RT-CUSTOMZ/WortUhr/Media/Rückseite.jpg

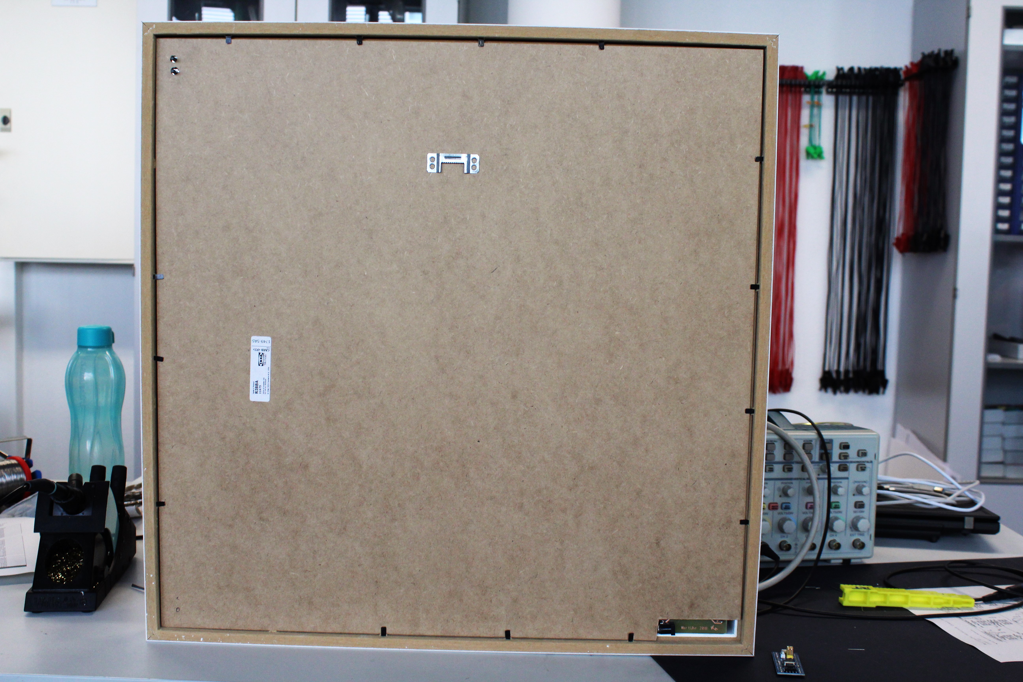
Media/Rückseite.jpg
