RT-CUSTOMZ/WortUhr/Media/Gitter Aufbau.png

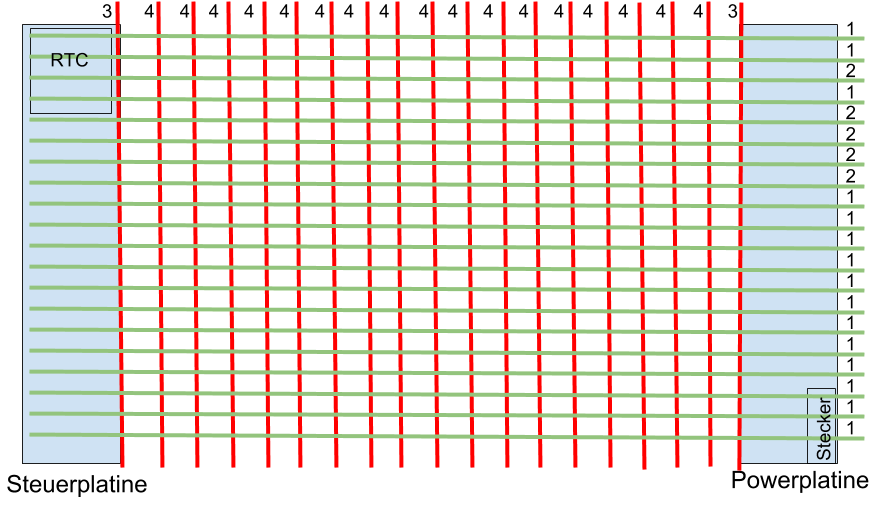
Media/Gitter Aufbau.png
