RT-CUSTOMZ/WortUhr/Hardware/Steuerplatine-Fertigung/Fertigungsplatine/Produktionsdaten_Steuerplatine_V2.2-Fertigung/Additional Documentation.pdf

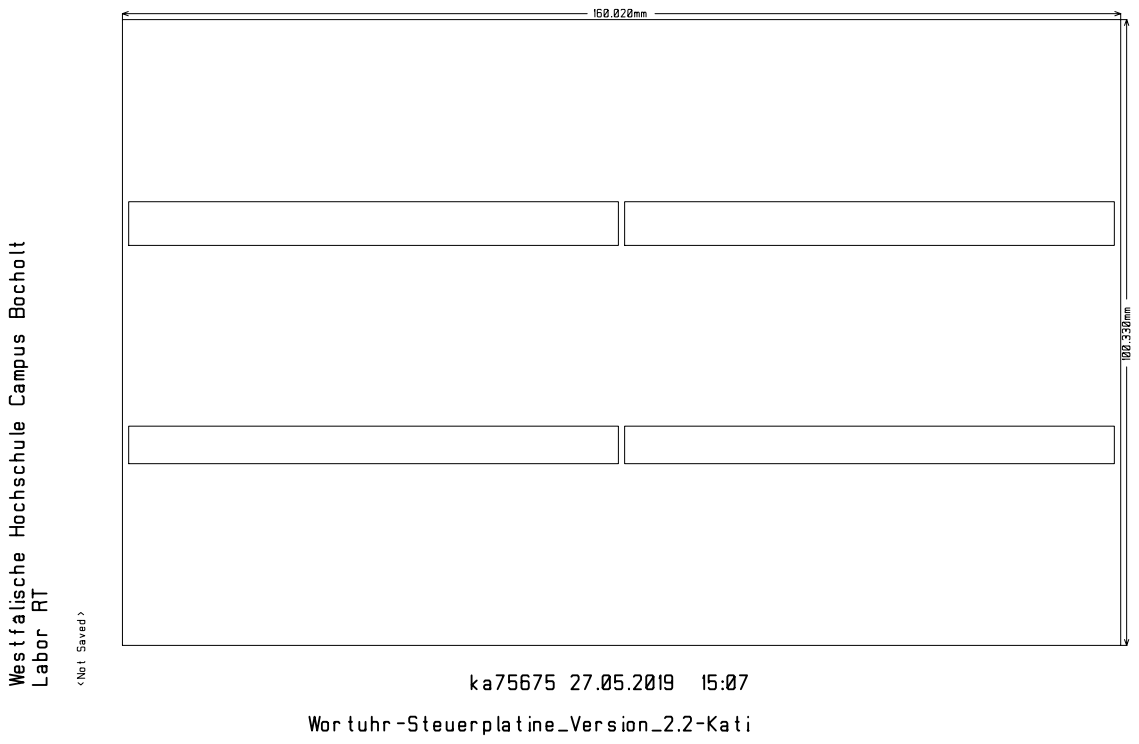
[picture p24: page 1]
