RT-CUSTOMZ/WortUhr/Hardware/Steuerplatine-Fertigung/Fertigungsplatine/Produktionsdaten_Steuerplatine_V2.2-Fertigung/Bottom Bestückungsplan.pdf

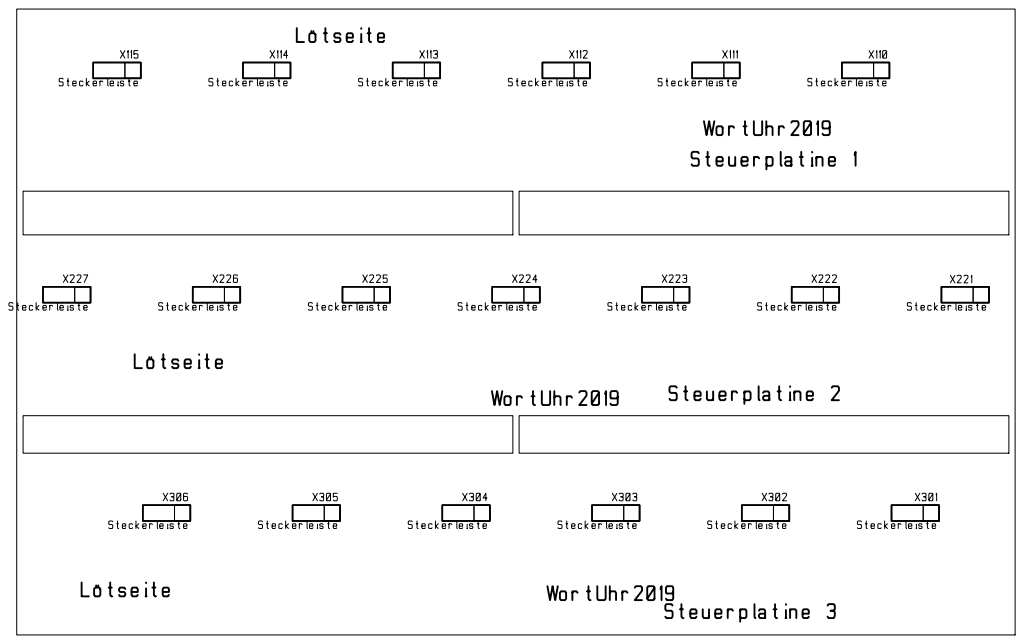
[picture p25: page 1]
