RT-CUSTOMZ/WortUhr/Hardware/Steuerplatine-Fertigung/Fertigungsplatine/Produktionsdaten_Steuerplatine_V2.2-Fertigung/Bottom Copper.pdf

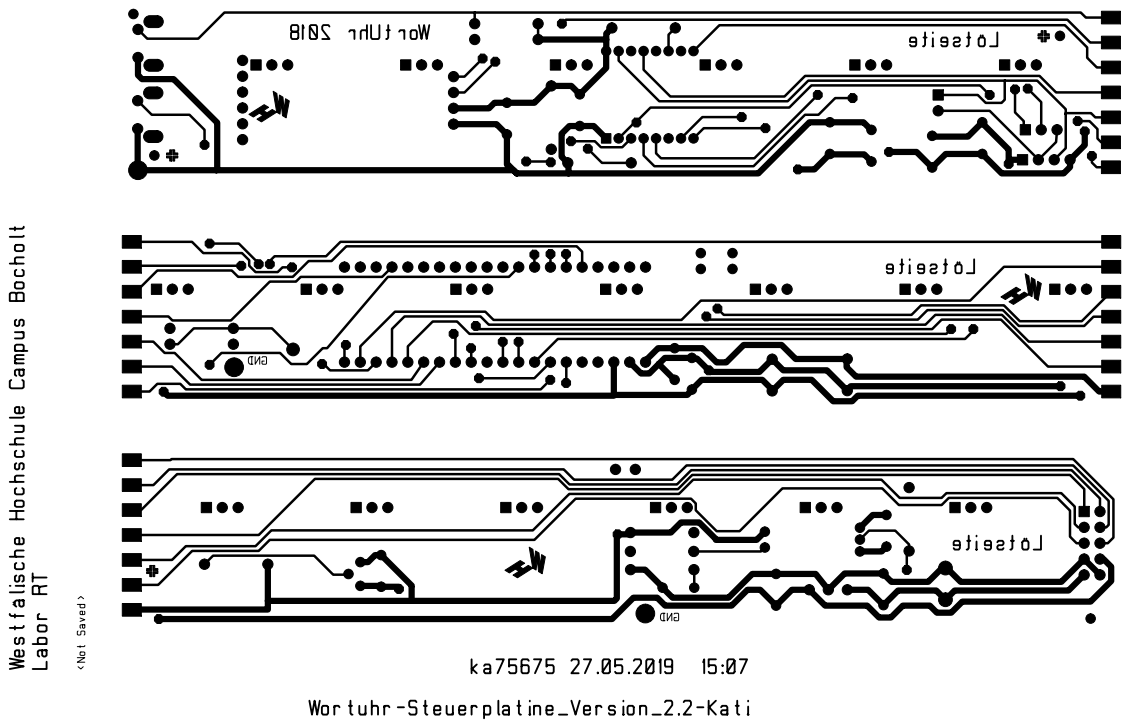
[picture p26: page 1]
