RT-CUSTOMZ/WortUhr/Hardware/Steuerplatine-Fertigung/Fertigungsplatine/Produktionsdaten_Steuerplatine_V2.2-Fertigung/Bottom Silkscreen.pdf

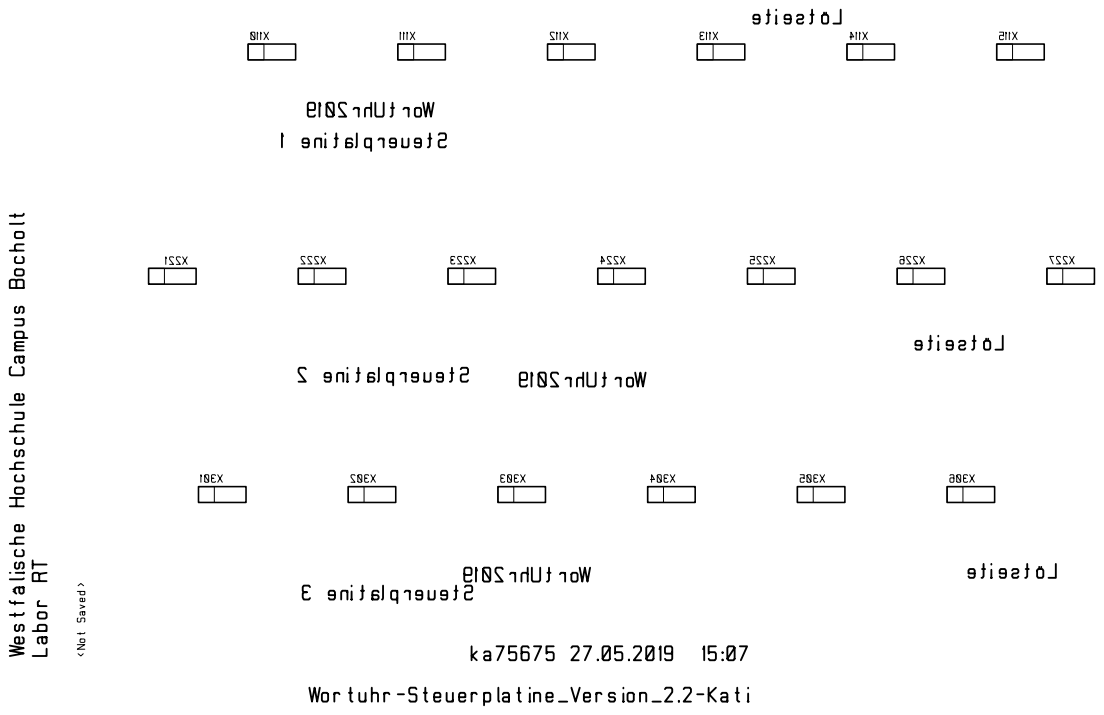
[picture p27: page 1]
