RT-CUSTOMZ/WortUhr/Hardware/Steuerplatine-Fertigung/Fertigungsplatine/Produktionsdaten_Steuerplatine_V2.2-Fertigung/Bottom Solderresist.pdf

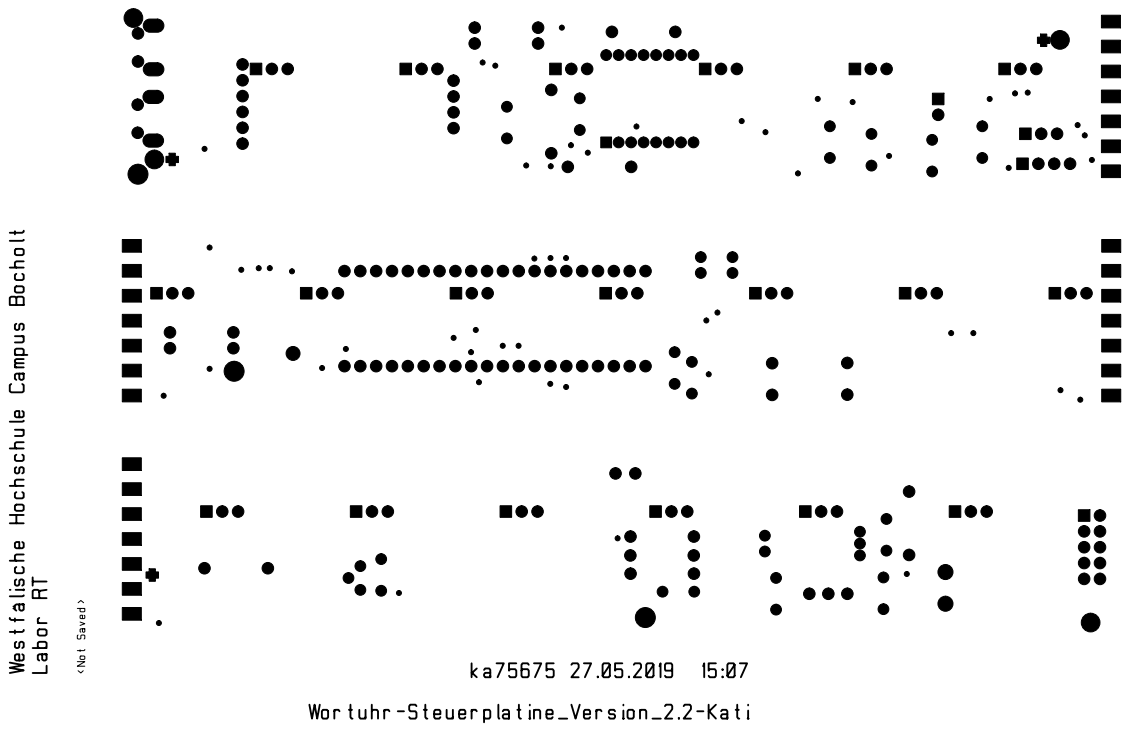
[picture p28: page 1]
