RT-CUSTOMZ/WortUhr/Hardware/Steuerplatine-Fertigung/Fertigungsplatine/Produktionsdaten_Steuerplatine_V2.2-Fertigung/Schaltplan-Fertigung-Steuer.pdf

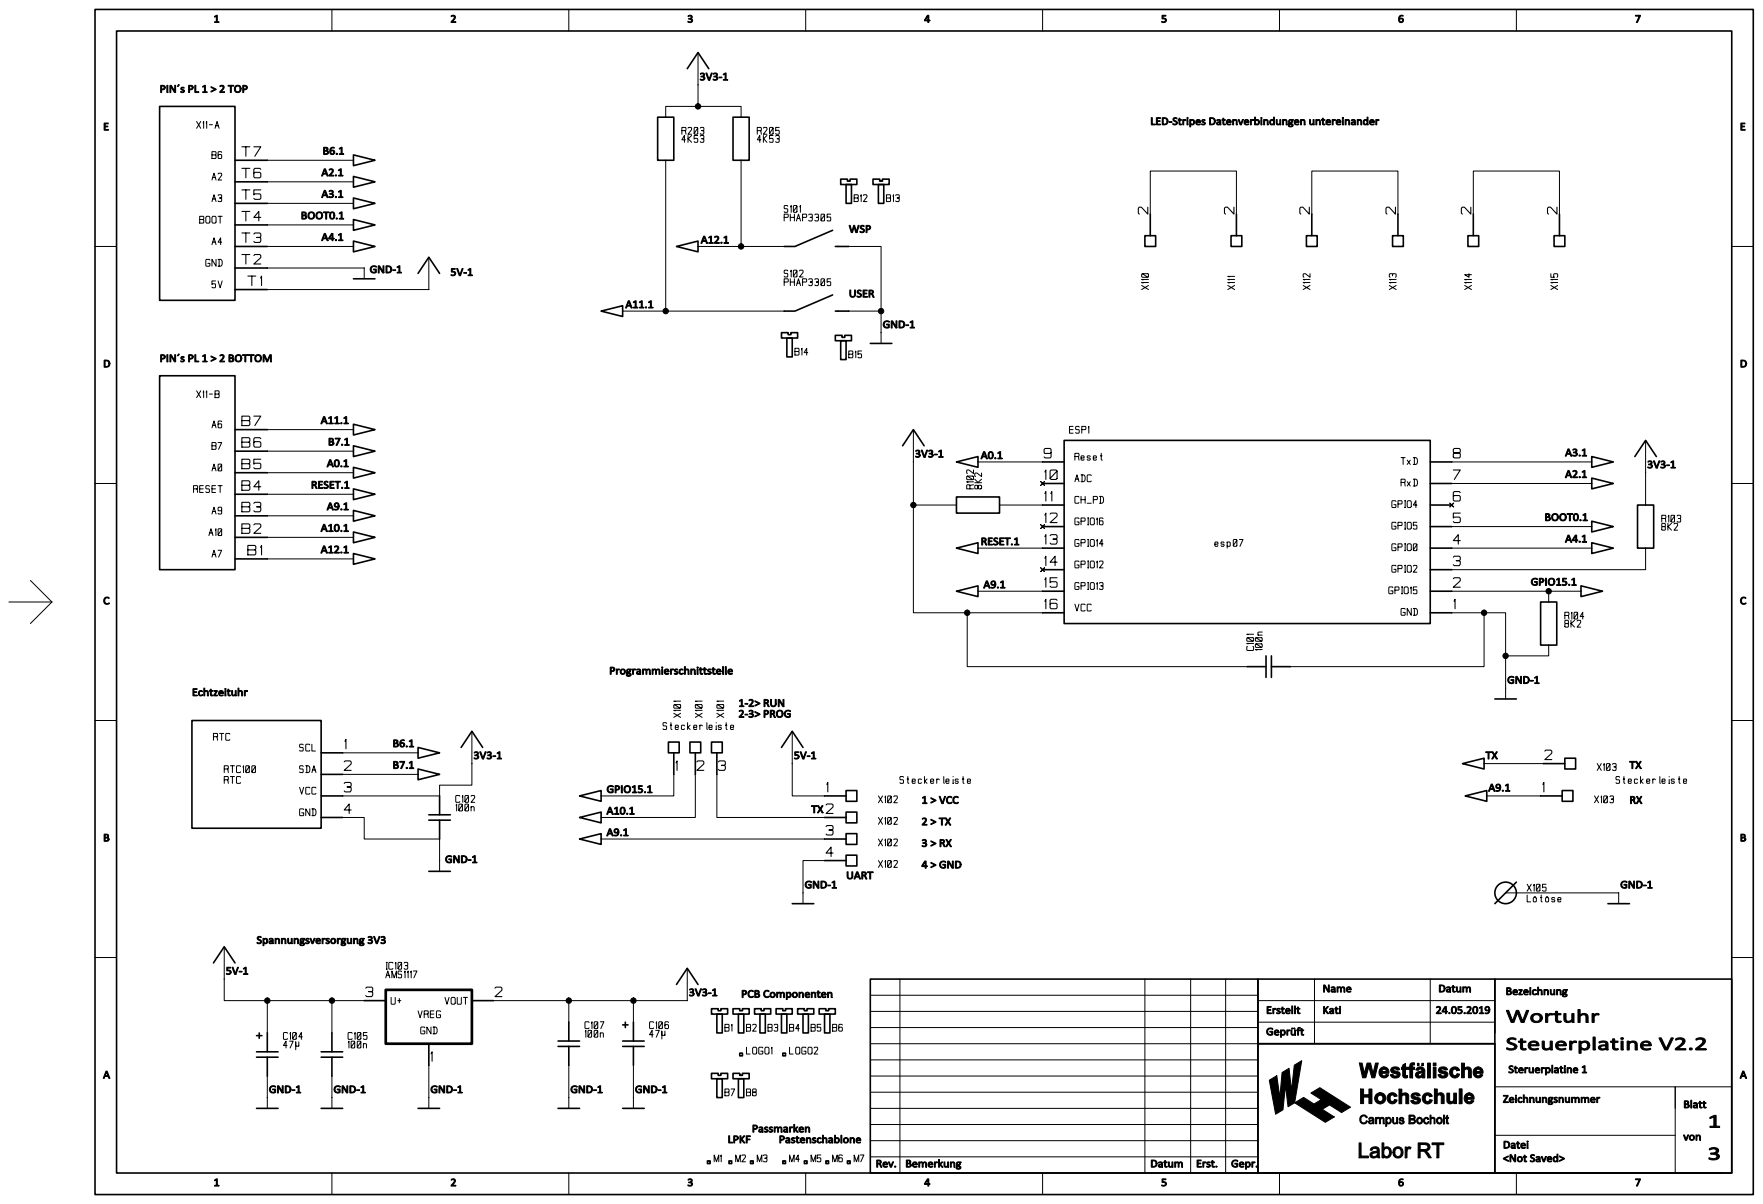
[picture p29: page 1]

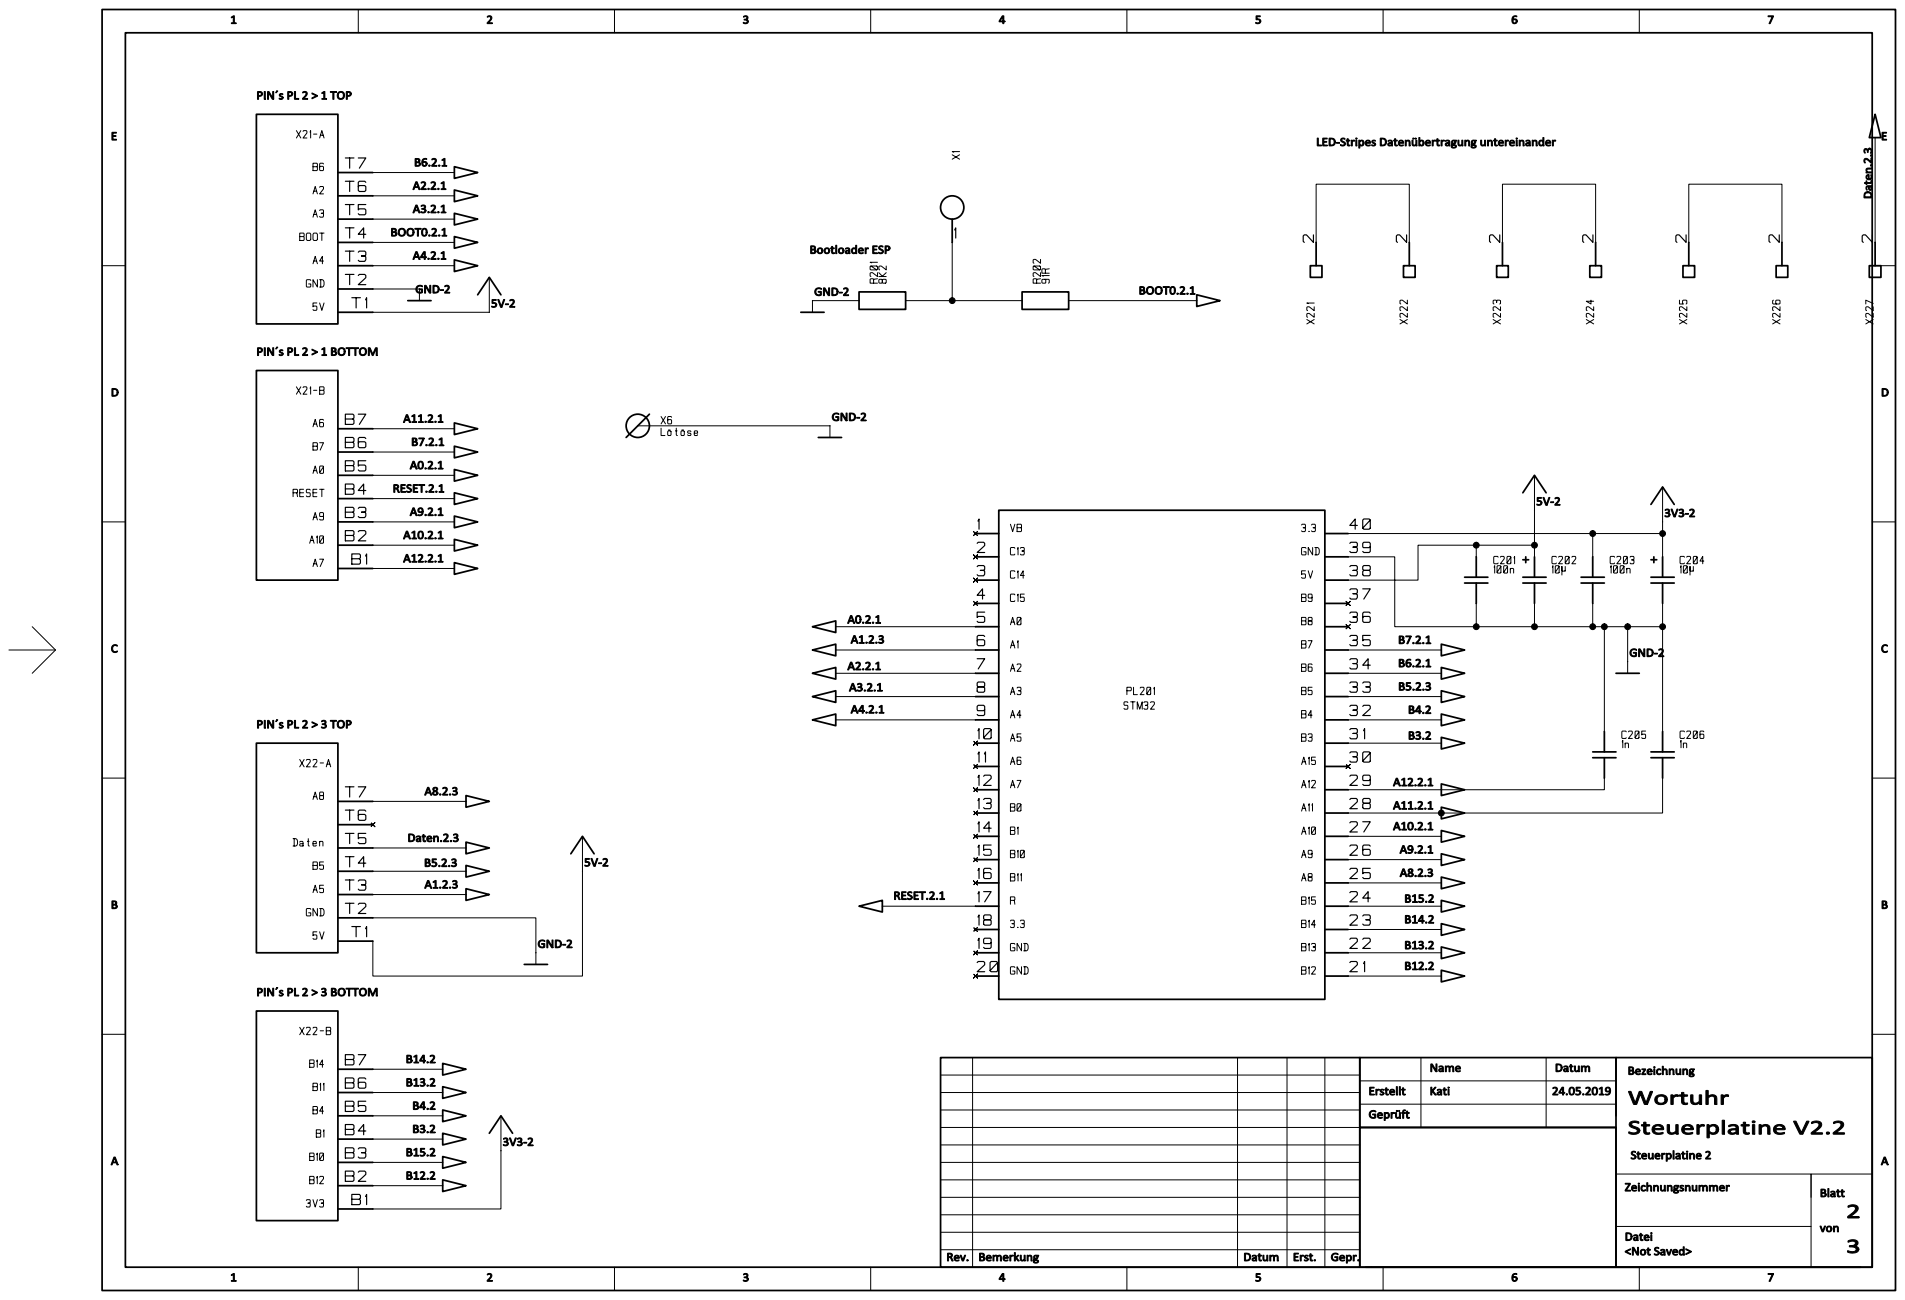
[picture p30: page 2]

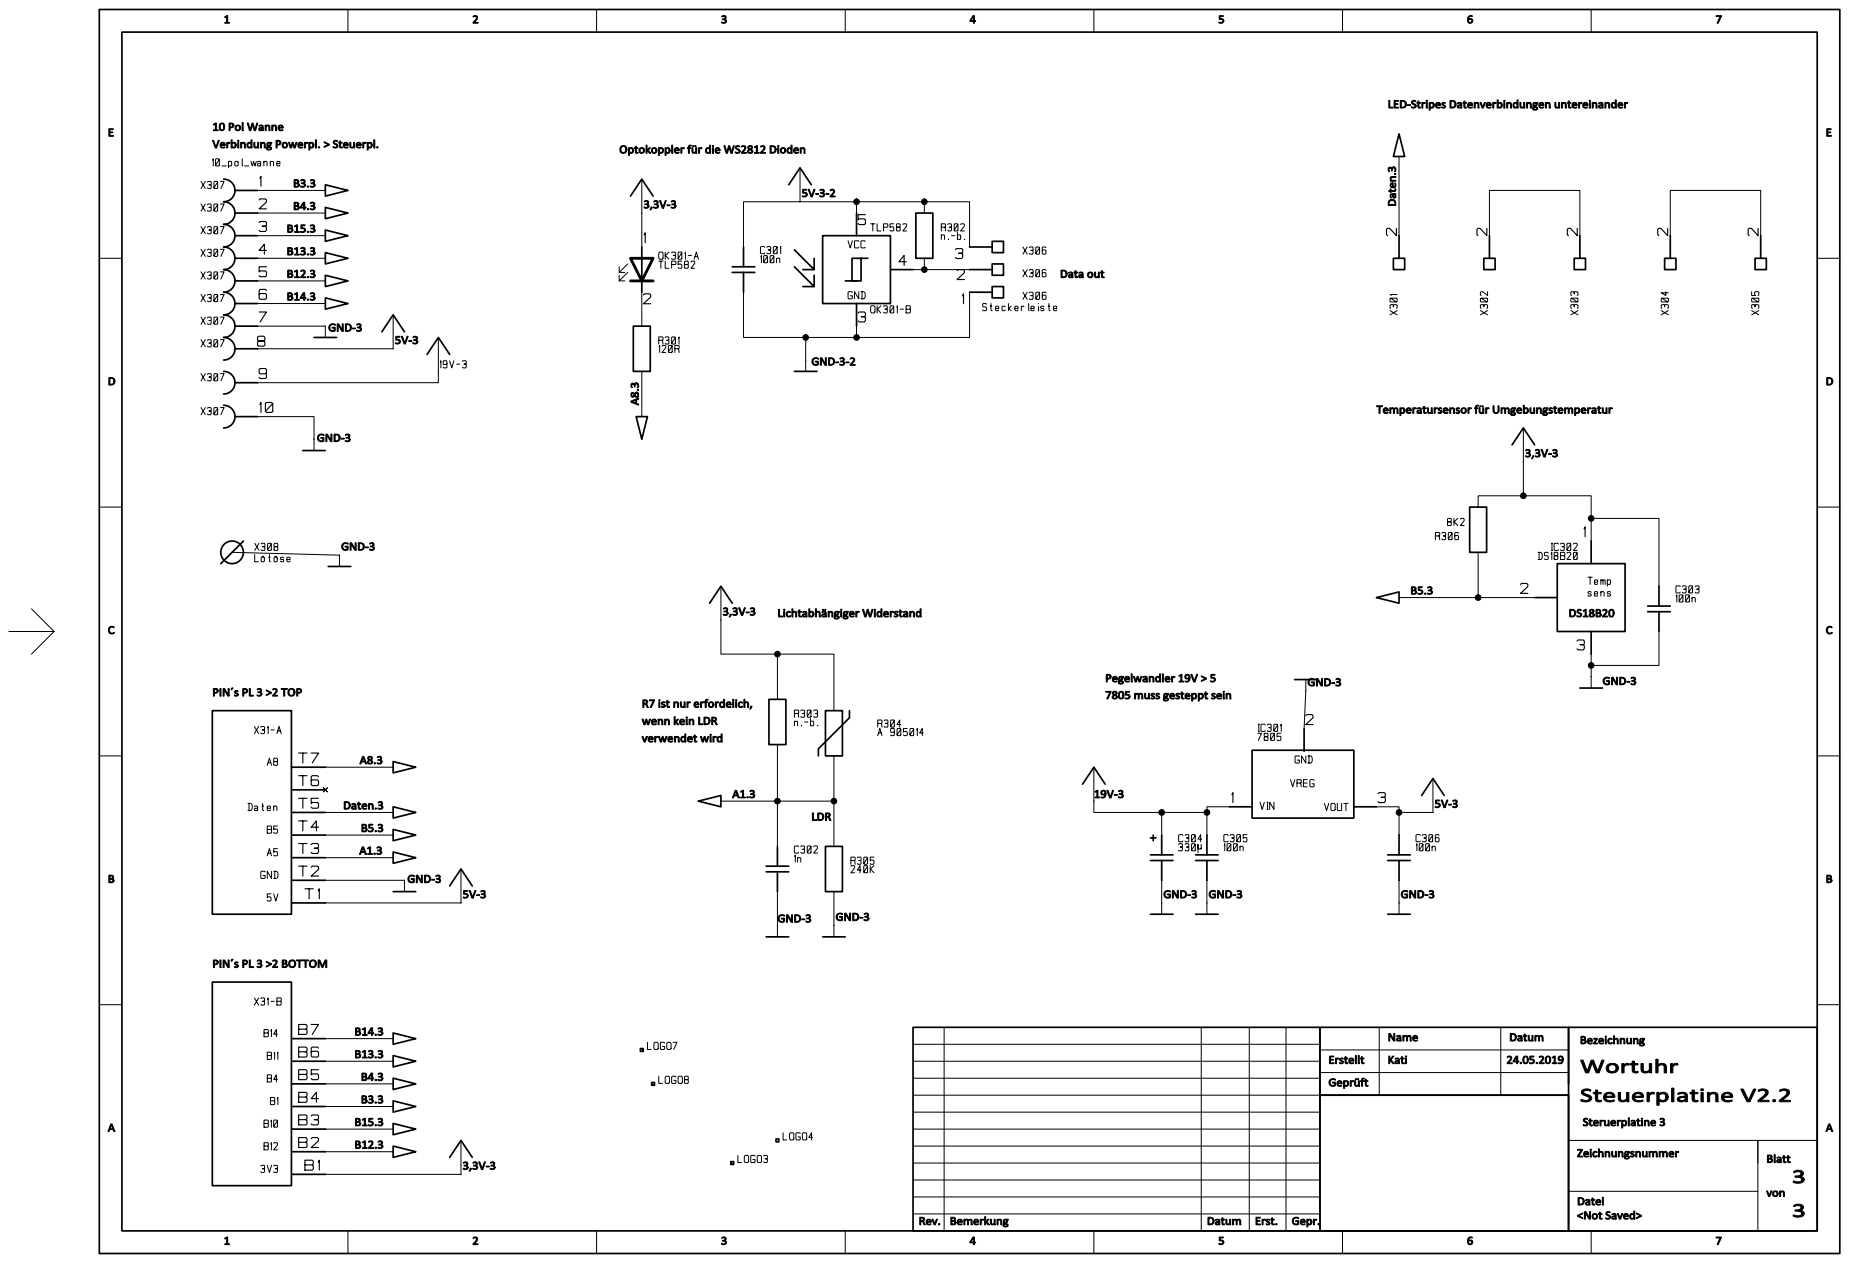
[picture p31: page 3]
