RT-CUSTOMZ/WortUhr/Lasercutter/Gitter-2x3-7x4.pdf

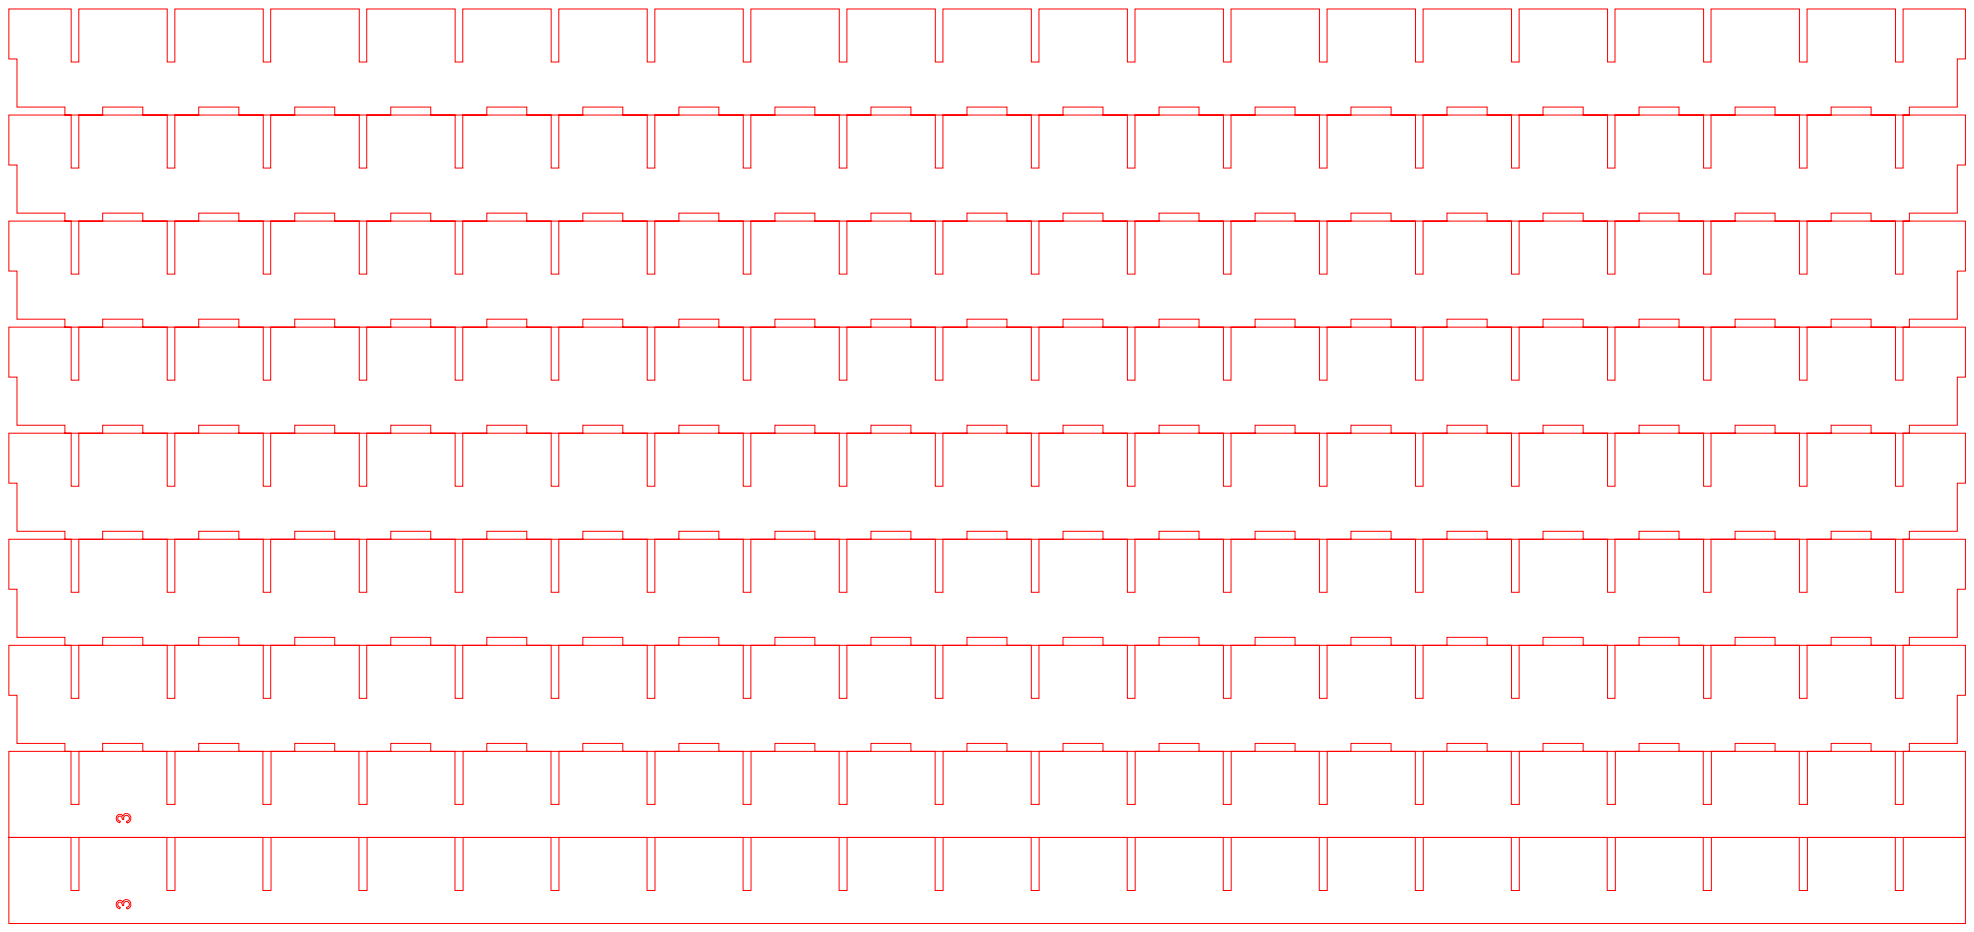
[picture p36: page 1]
