RT-CUSTOMZ/WortUhr/Lasercutter/Gitter-5x1-5x2.pdf

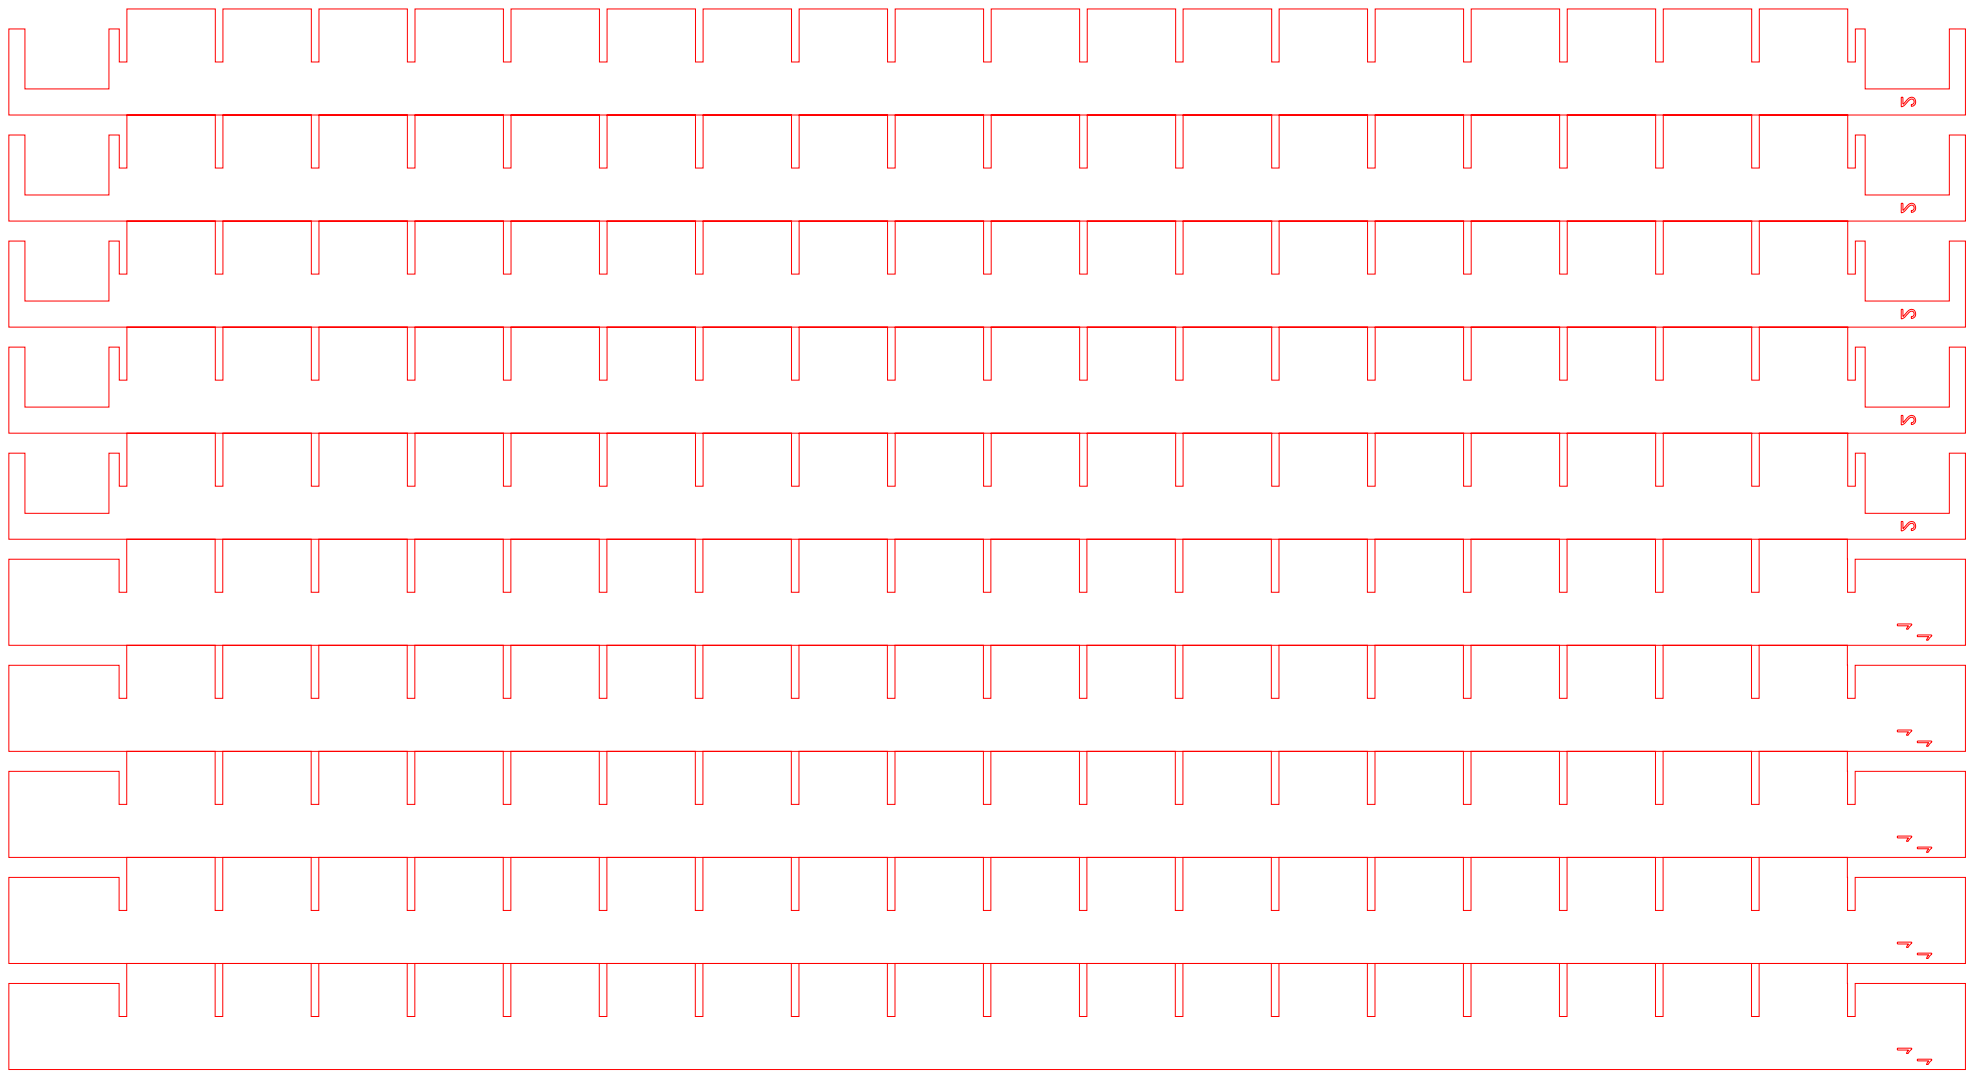
[picture p37: page 1]
