RT-CUSTOMZ/WortUhr/Hardware/Alt/Netzteilplatinen V1.1/Doku Bestückungsplan BOTTOM.pdf

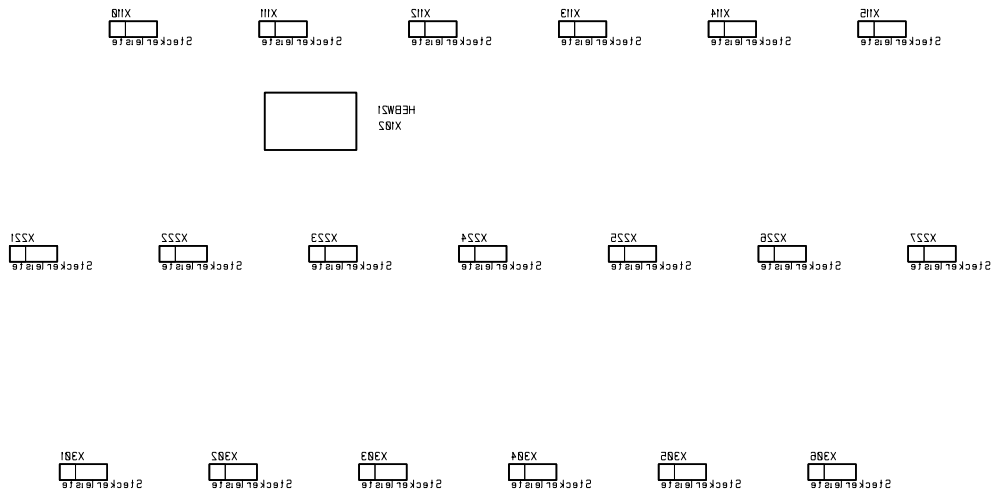
[picture p38: page 1]
