RT-CUSTOMZ/WortUhr/Hardware/Alt/Netzteilplatinen V1.1/Doku Bestückungsplan TOP.pdf

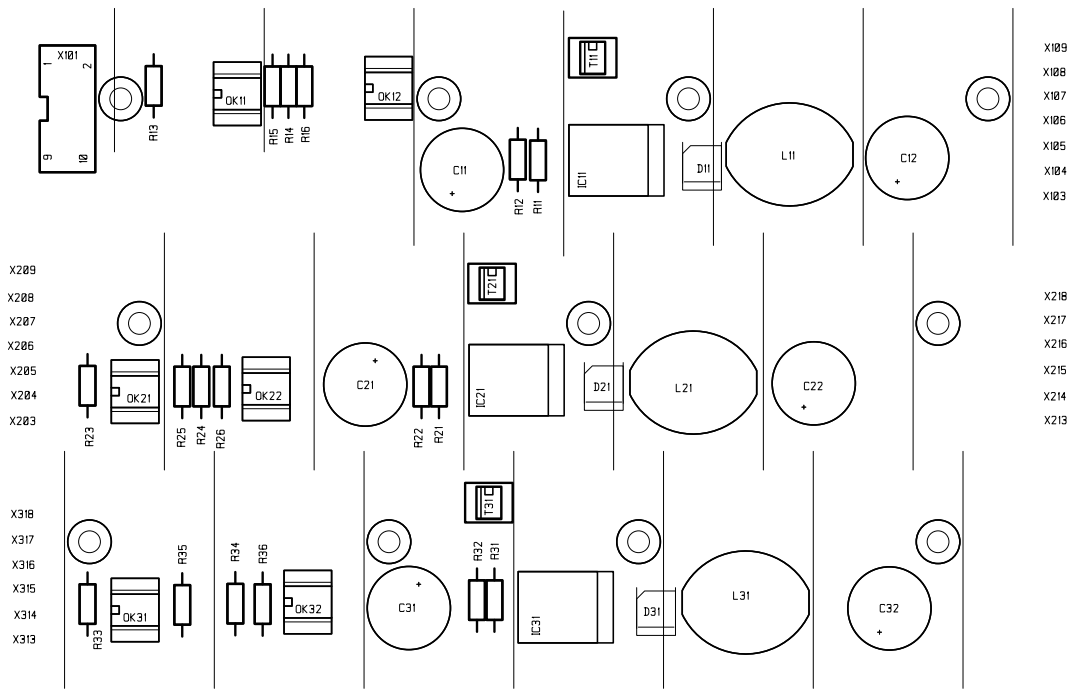
[picture p39: page 1]
