RT-CUSTOMZ/WortUhr/Hardware/Alt/Netzteilplatinen V1.1/Doku Routingübertsicht BOTTOM.pdf

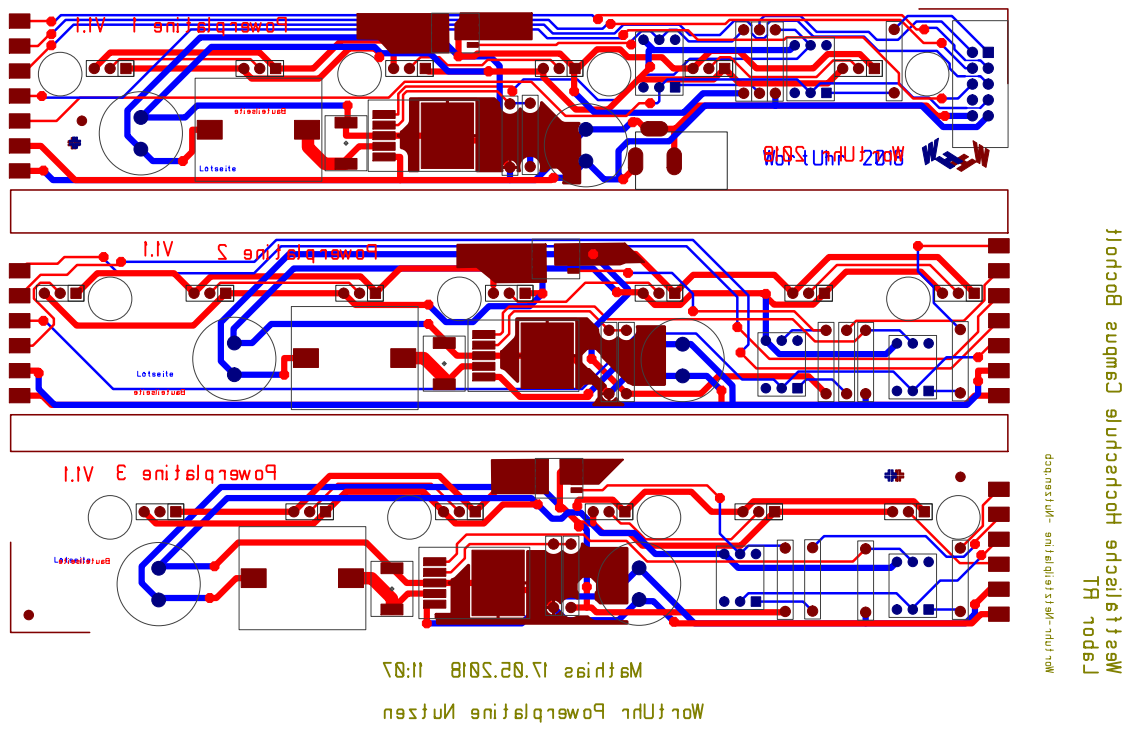
[picture p40: page 1]
