RT-CUSTOMZ/WortUhr/Hardware/Alt/Netzteilplatinen V1.1/Doku Routingübertsicht TOP.pdf

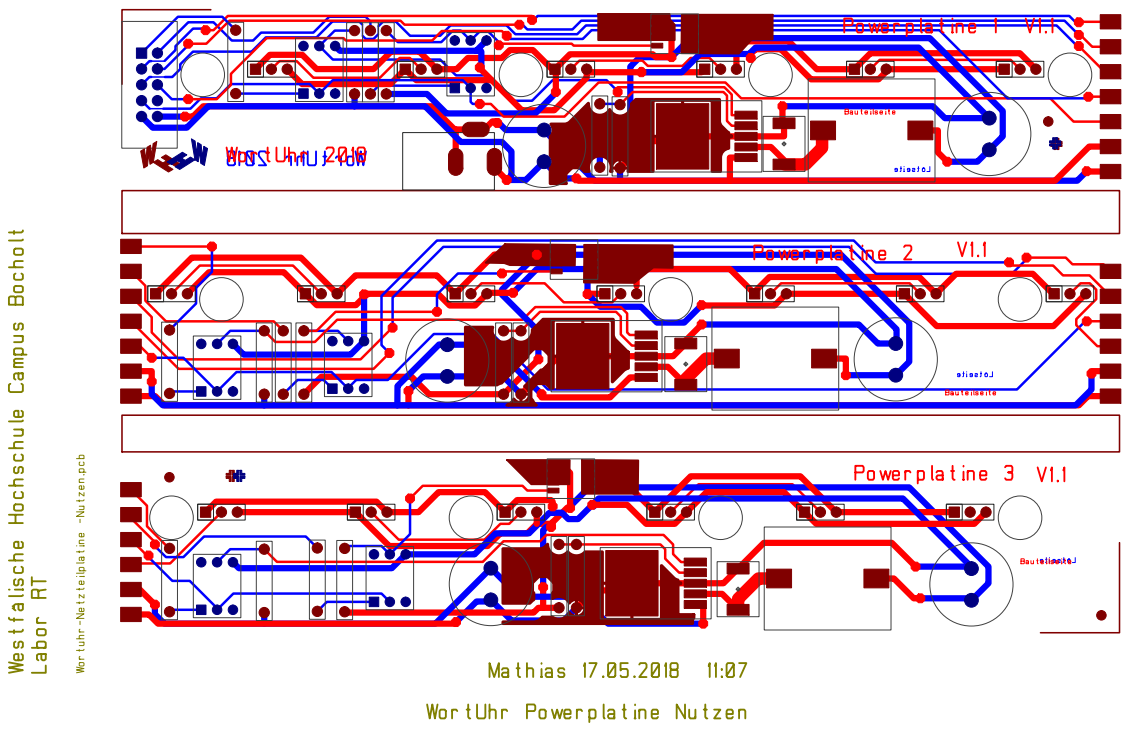
[picture p41: page 1]
