RT-CUSTOMZ/WortUhr/Hardware/Alt/Netzteilplatinen V1.1/Film Bestückungsplan TOP in Kupfer.pdf

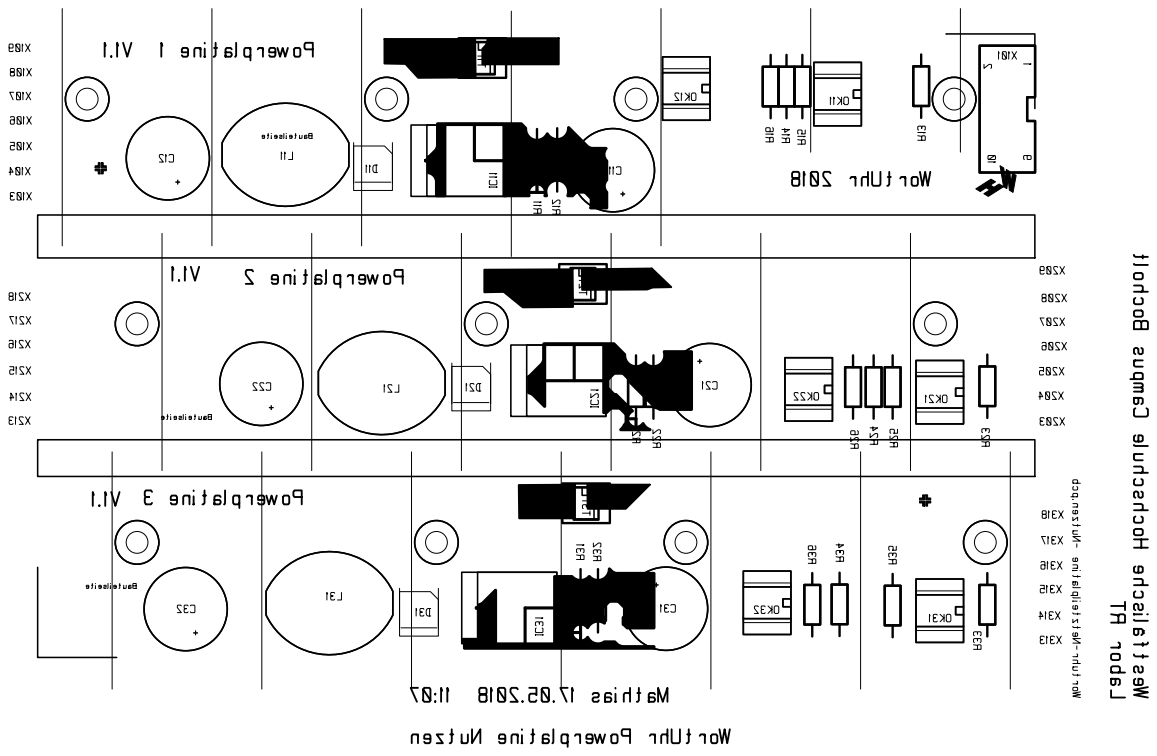
[picture p42: page 1]
