RT-CUSTOMZ/WortUhr/Hardware/Alt/Netzteilplatinen V1.1/FILM BOTTOM.pdf

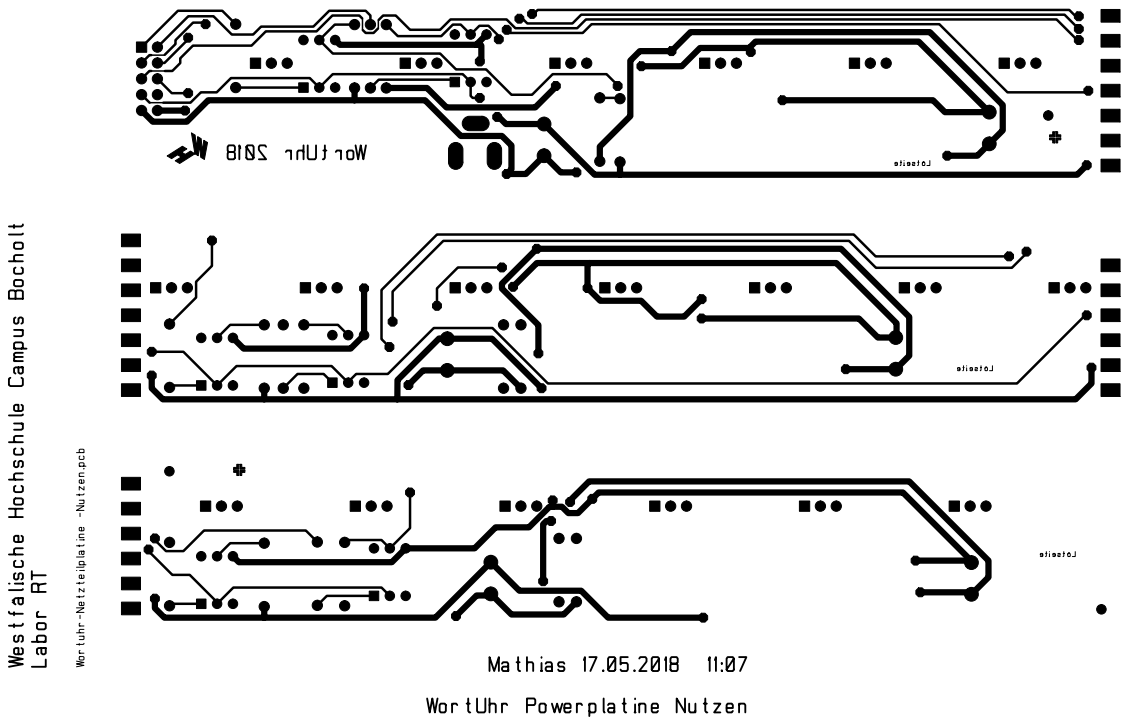
[picture p43: page 1]
