RT-CUSTOMZ/WortUhr/Hardware/Alt/Netzteilplatinen V1.1/FILM TOP.pdf

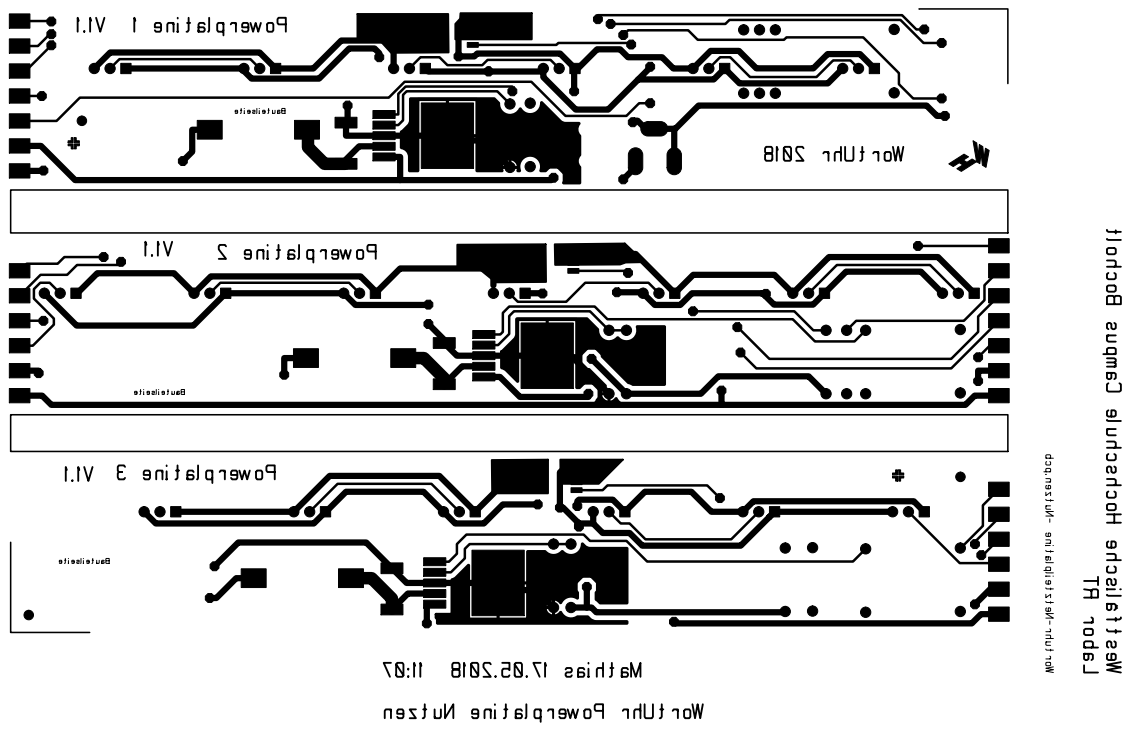
[picture p44: page 1]
