RT-CUSTOMZ/WortUhr/Hardware/Alt/Netzteilplatinen V1.1/Wortuhr-Netzteilplatine -Nutzen-Bestück Bottom.pdf

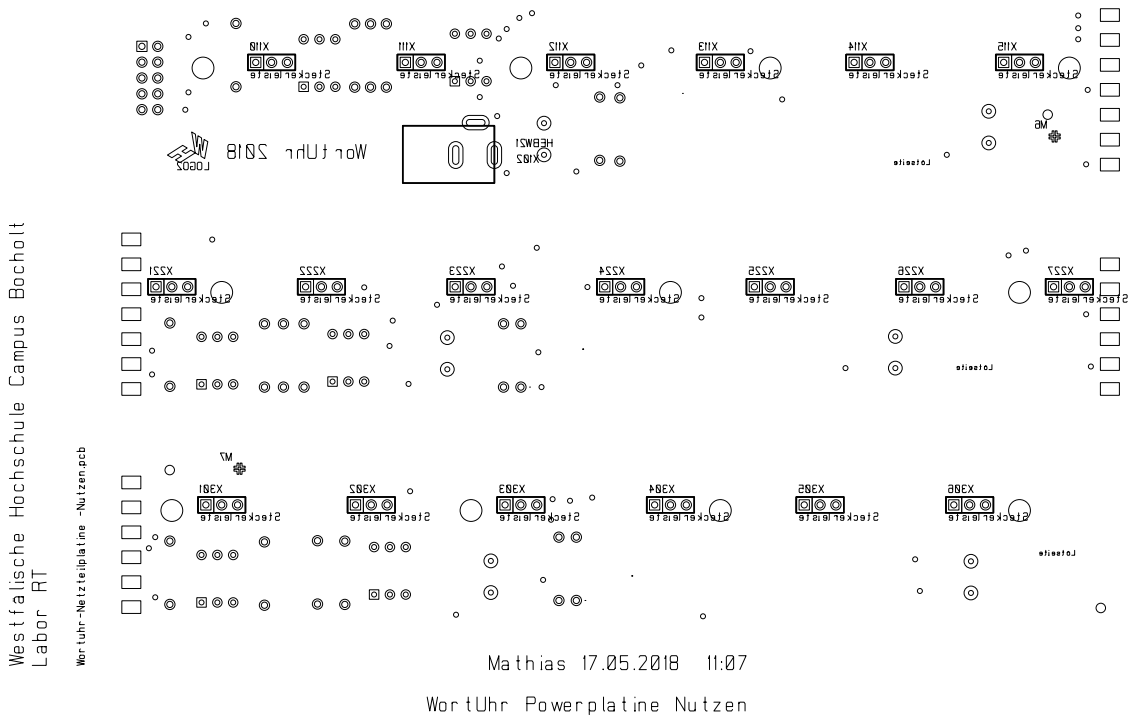
[picture p45: page 1]
