RT-CUSTOMZ/WortUhr/Hardware/Alt/Netzteilplatinen V1.1/Wortuhr-Netzteilplatine -Nutzen-Bestück Top.pdf

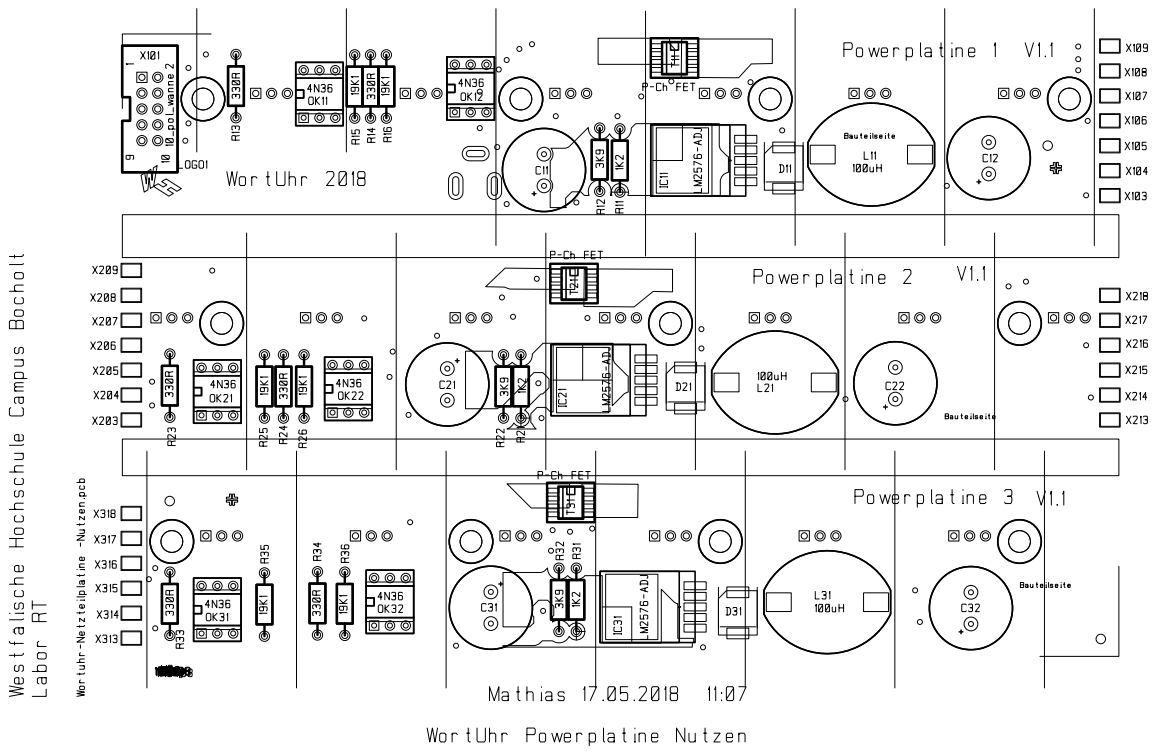
[picture p46: page 1]
