RT-CUSTOMZ/WortUhr/Hardware/Alt/Netzteilplatinen V1.1/Wortuhr-Netzteilplatine -Nutzen-Schematic.pdf

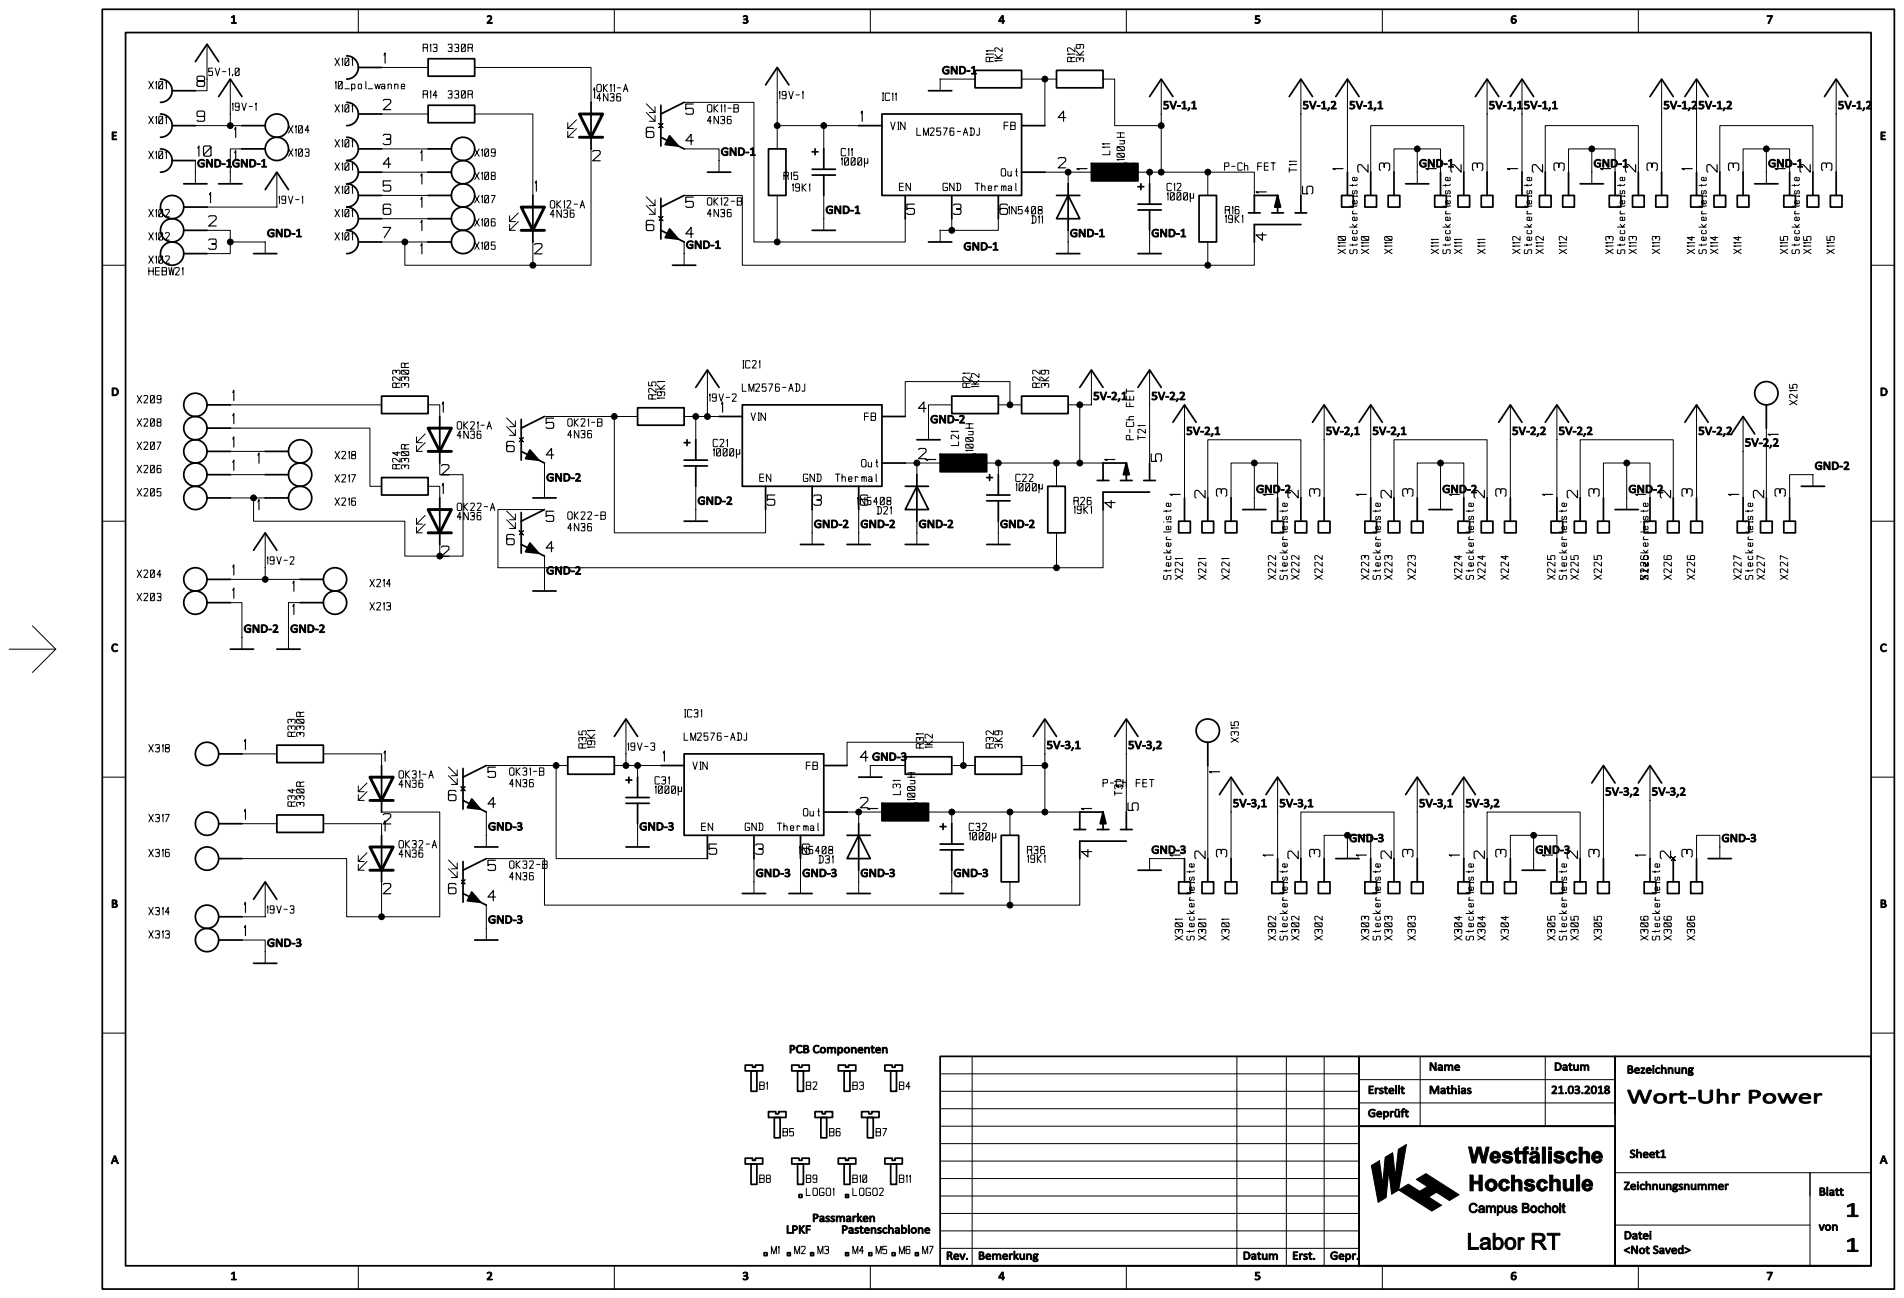
[picture p47: page 1]
