RT-CUSTOMZ/WortUhr/Hardware/Alt/Netzteilplatinen V1.1/Wortuhr-Netzteilplatine -Nutzen-Viaplan.pdf

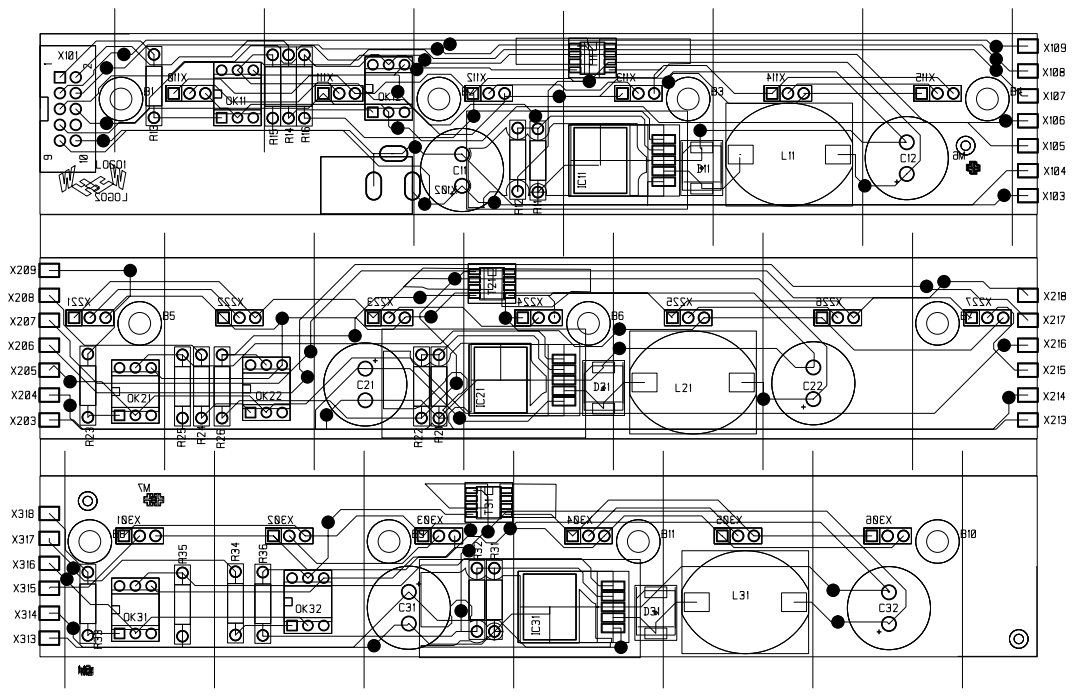
[picture p48: page 1]
