RT-CUSTOMZ/WortUhr/Hardware/Alt/Steuerplatinen Produktionsdaten V1.1/Doku Bestückungsplan BOTTOM.pdf

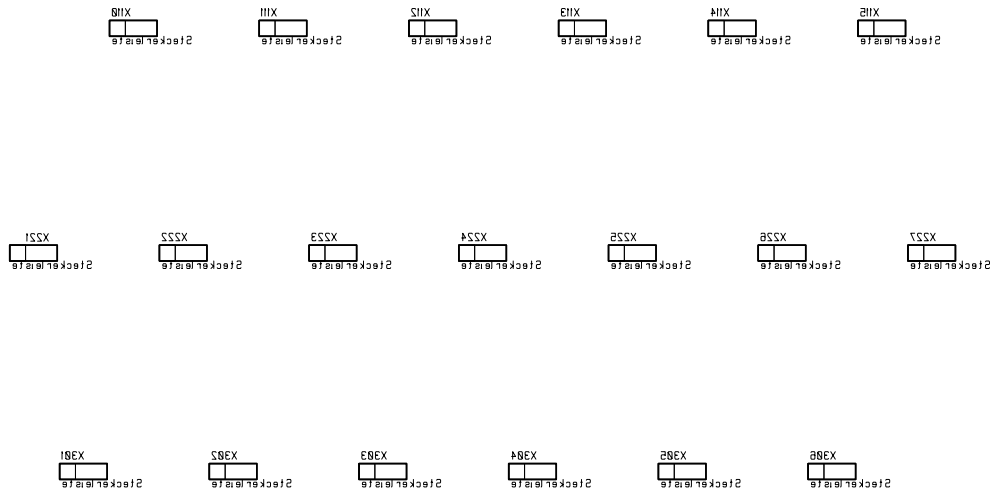
[picture p49: page 1]
