RT-CUSTOMZ/WortUhr/Hardware/Alt/Steuerplatinen Produktionsdaten V1.1/Doku Bestückungsplan TOP.pdf

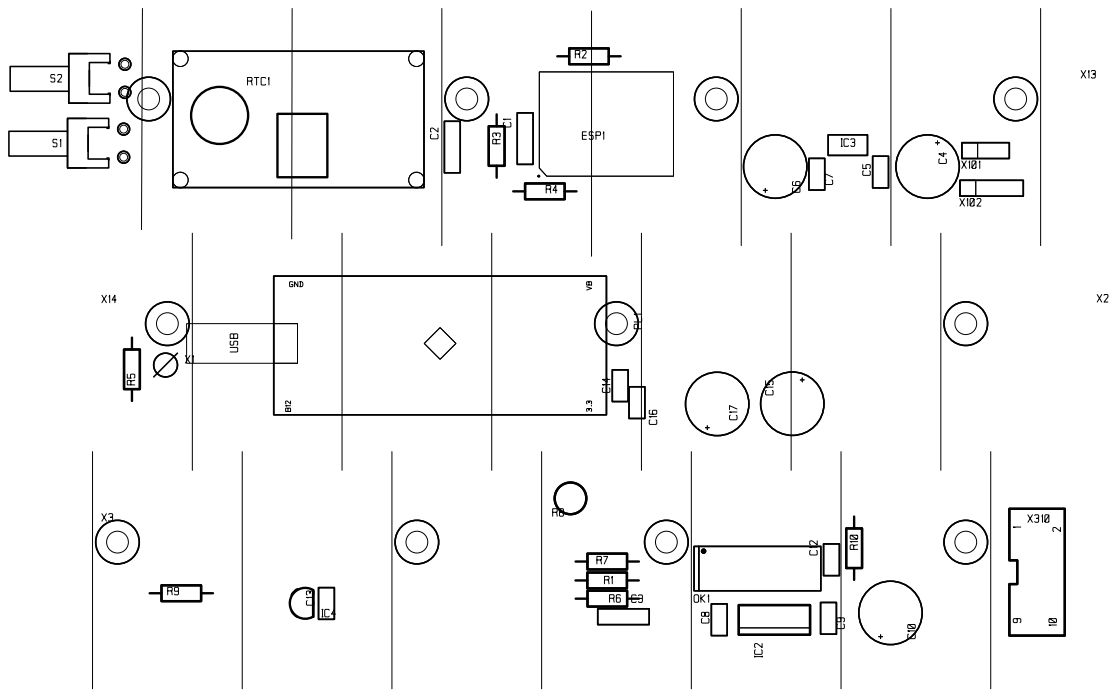
[picture p50: page 1]
