RT-CUSTOMZ/WortUhr/Hardware/Alt/Steuerplatinen Produktionsdaten V1.1/Doku Routingübertsicht BOTTOM.pdf

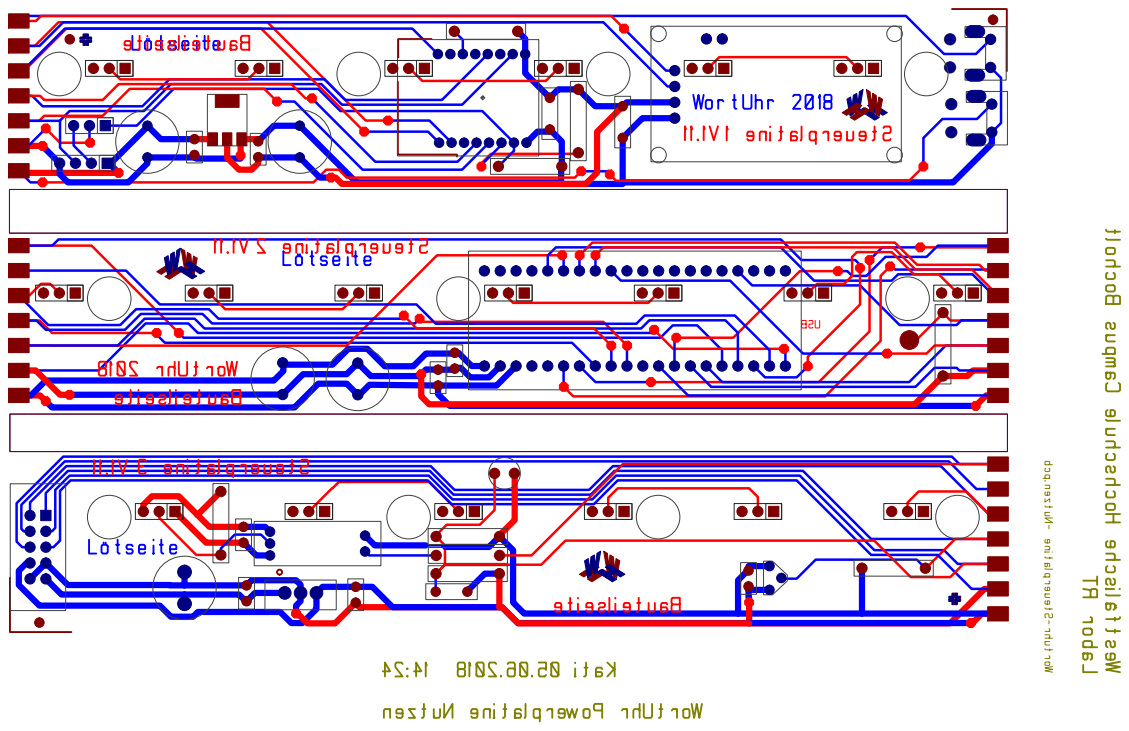
[picture p51: page 1]
