RT-CUSTOMZ/WortUhr/Hardware/Alt/Steuerplatinen Produktionsdaten V1.1/Doku Routingübertsicht TOP.pdf

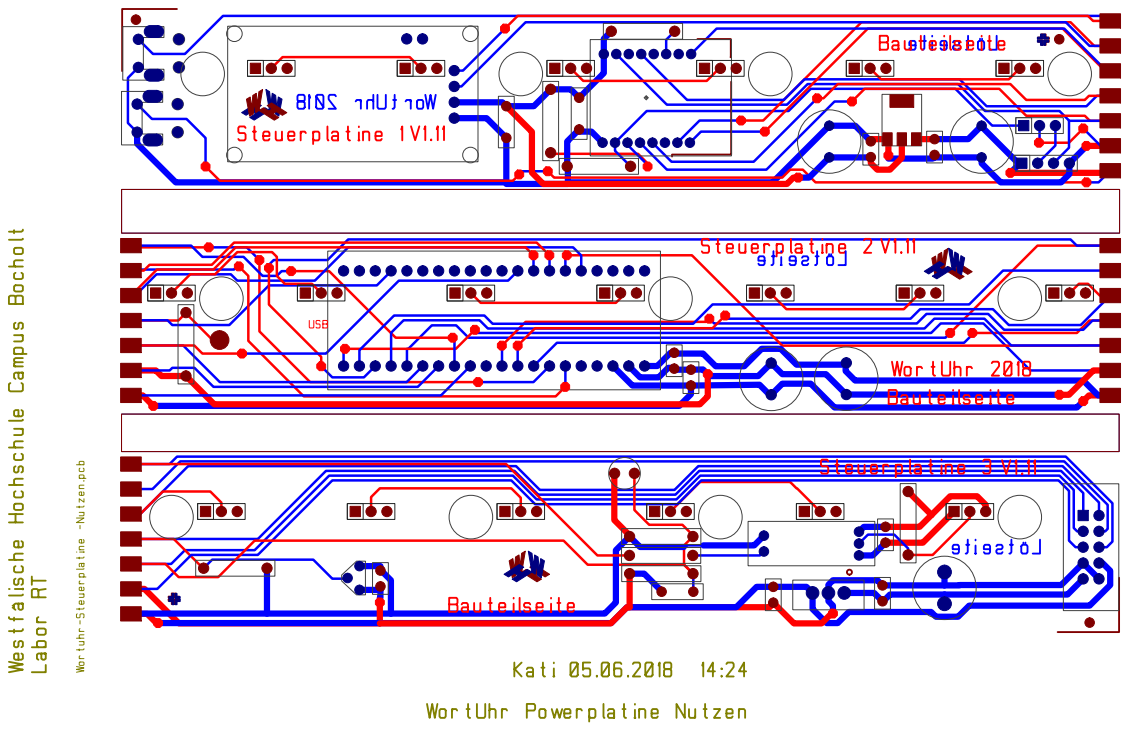
[picture p52: page 1]
