RT-CUSTOMZ/WortUhr/Hardware/Alt/Steuerplatinen Produktionsdaten V1.1/Film Bestückungsplan TOP in Kupfer.pdf

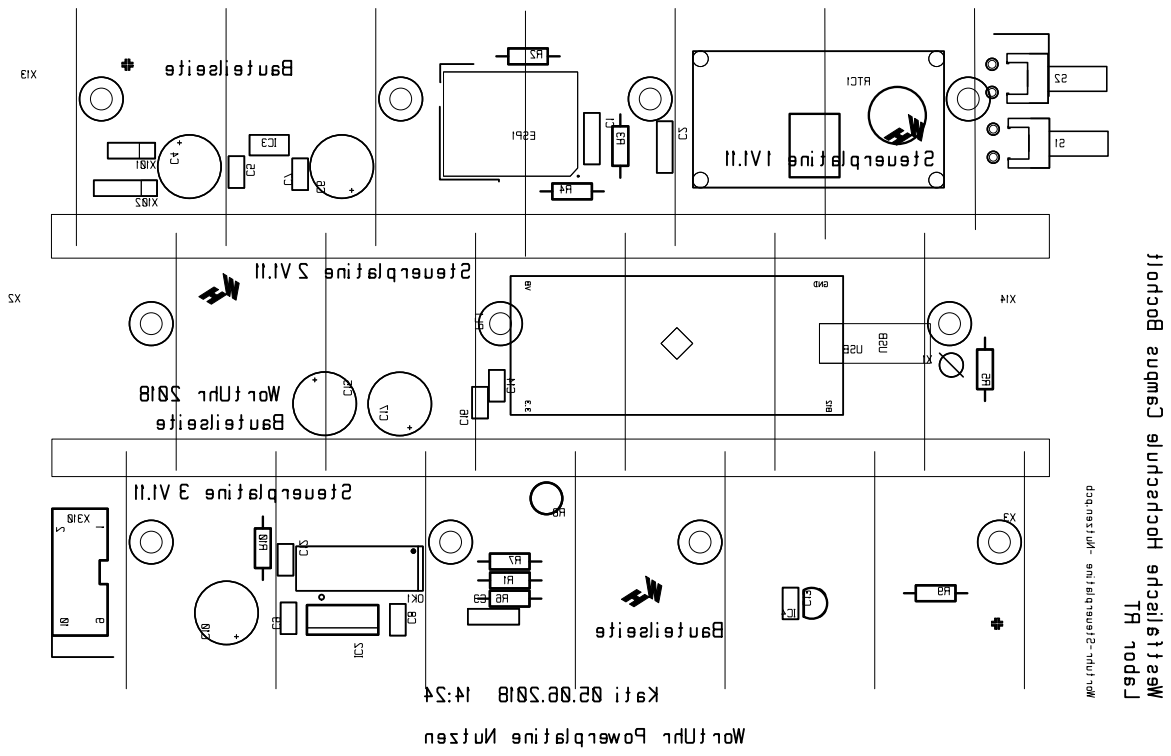
[picture p53: page 1]
