RT-CUSTOMZ/WortUhr/Hardware/Alt/Steuerplatinen Produktionsdaten V1.1/FILM BOTTOM.pdf

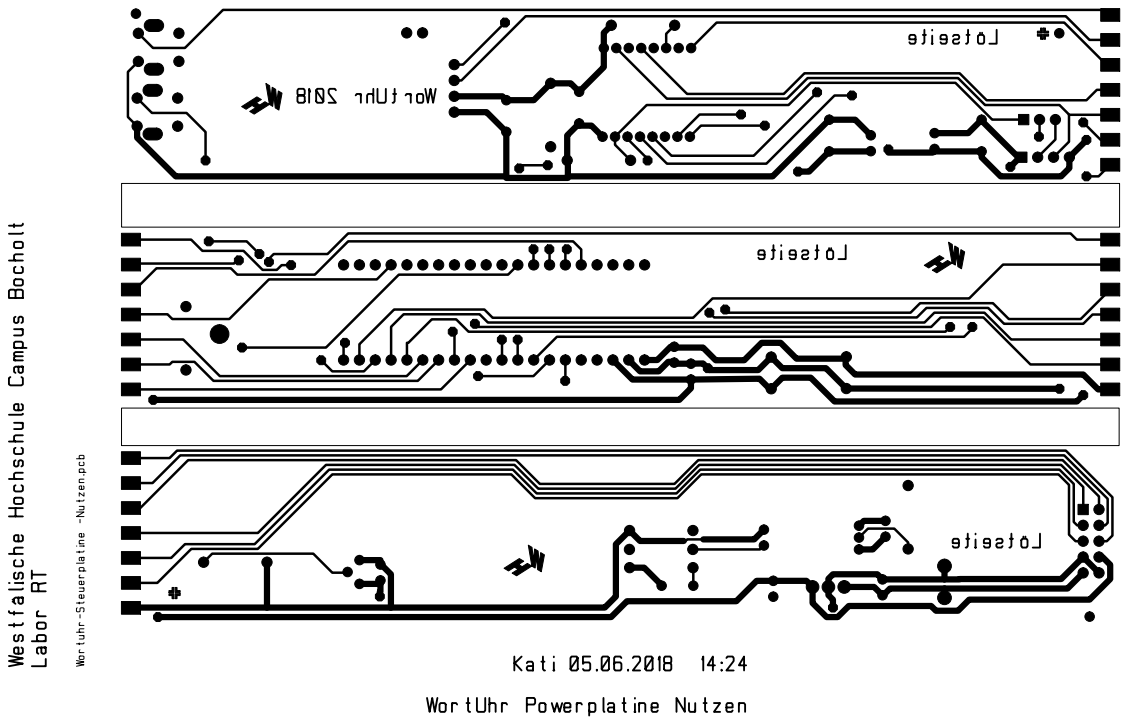
[picture p54: page 1]
