RT-CUSTOMZ/WortUhr/Hardware/Alt/Steuerplatinen Produktionsdaten V1.1/FILM TOP.pdf

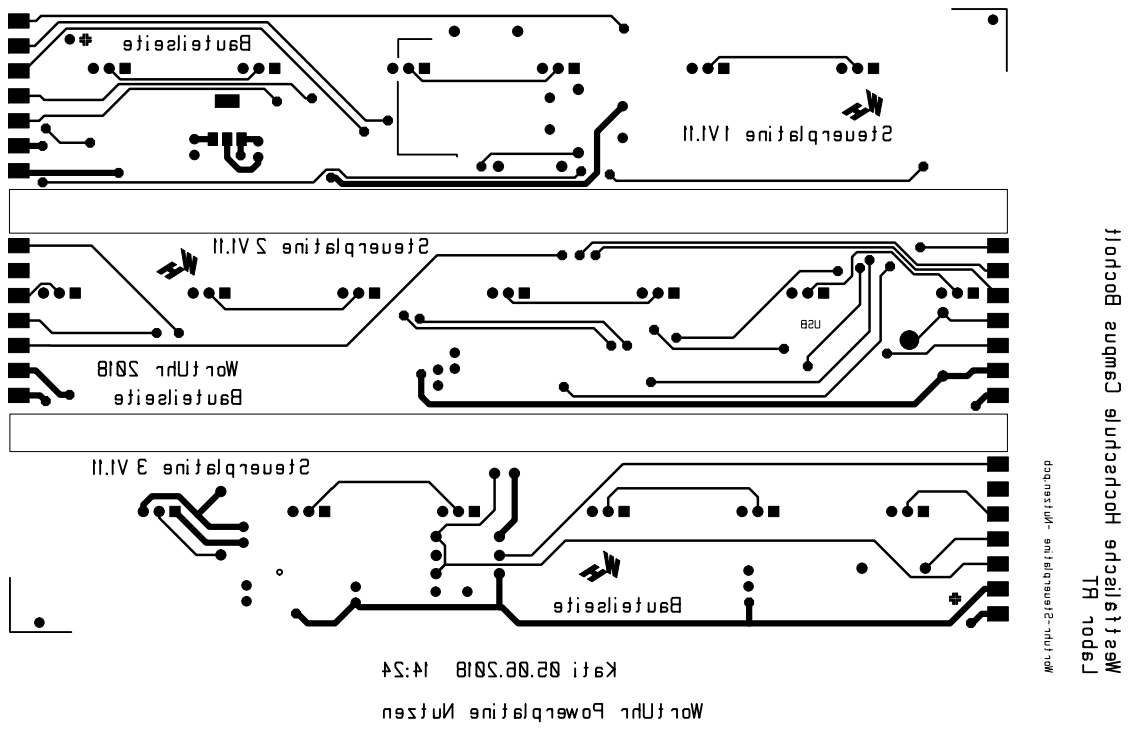
[picture p55: page 1]
