RT-CUSTOMZ/WortUhr/Hardware/Alt/Steuerplatinen Produktionsdaten V1.1/Wortuhr-Steuerplatine-NutzenNEU-ohne BO- Bestück Bottom.pdf

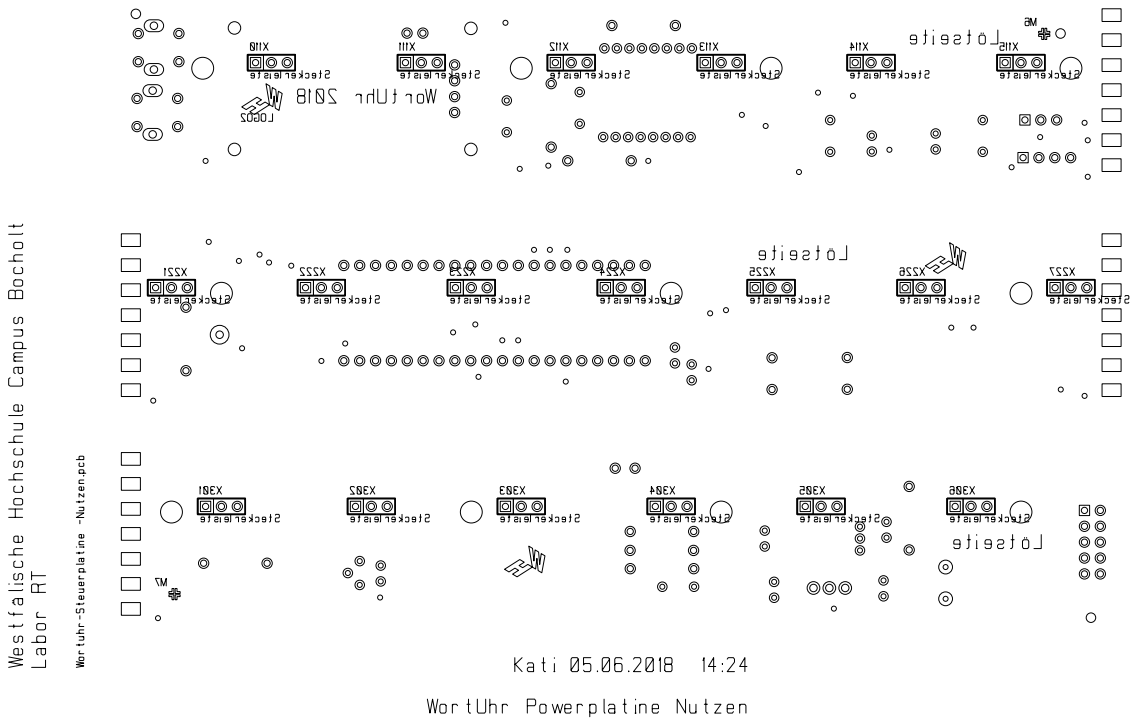
[picture p56: page 1]
