RT-CUSTOMZ/WortUhr/Hardware/Alt/Steuerplatinen Produktionsdaten V1.1/Wortuhr-Steuerplatine-NutzenNEU-ohne BO- Bestück Top.pdf

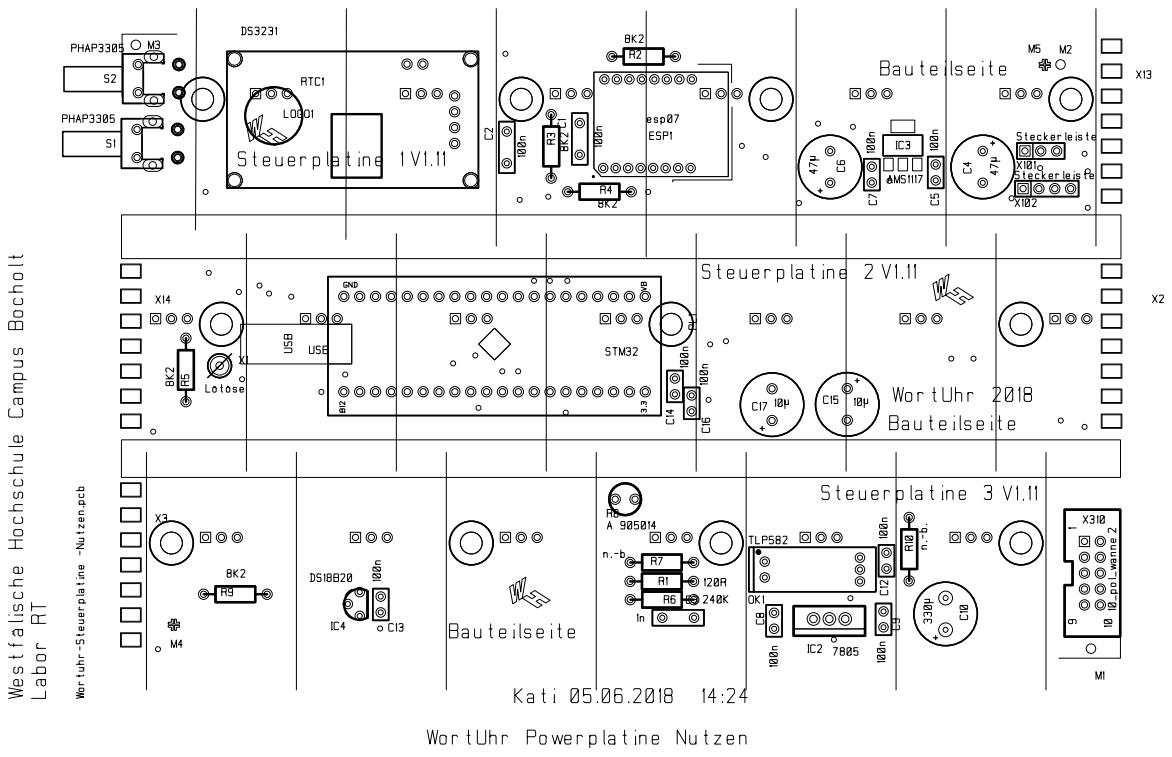
[picture p57: page 1]
