RT-CUSTOMZ/WortUhr/Hardware/Alt/Steuerplatinen Produktionsdaten V1.1/Wortuhr-Steuerplatine-NutzenNEU-ohne BO- Schematic.pdf

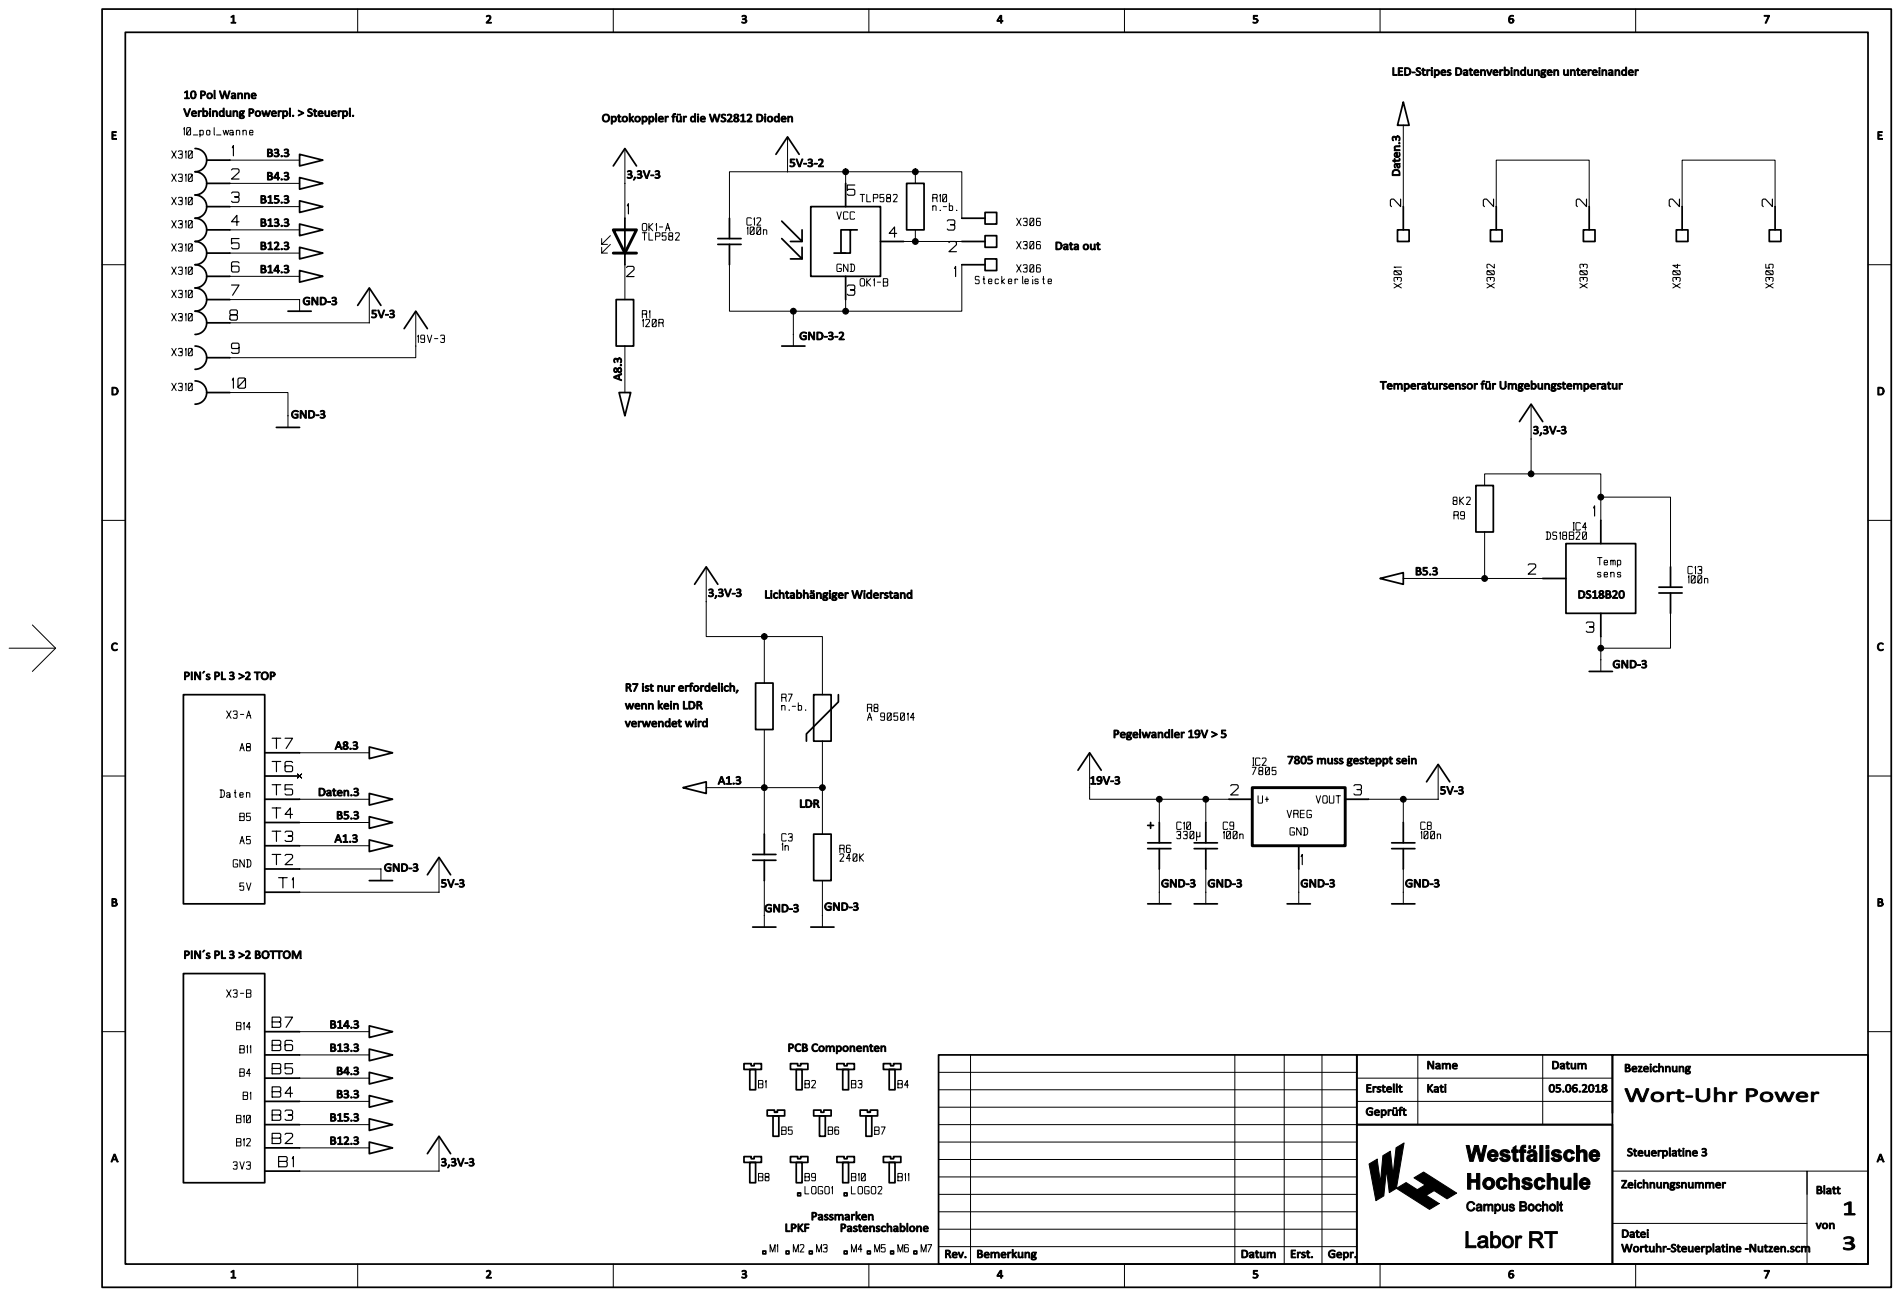
[picture p58: page 1]

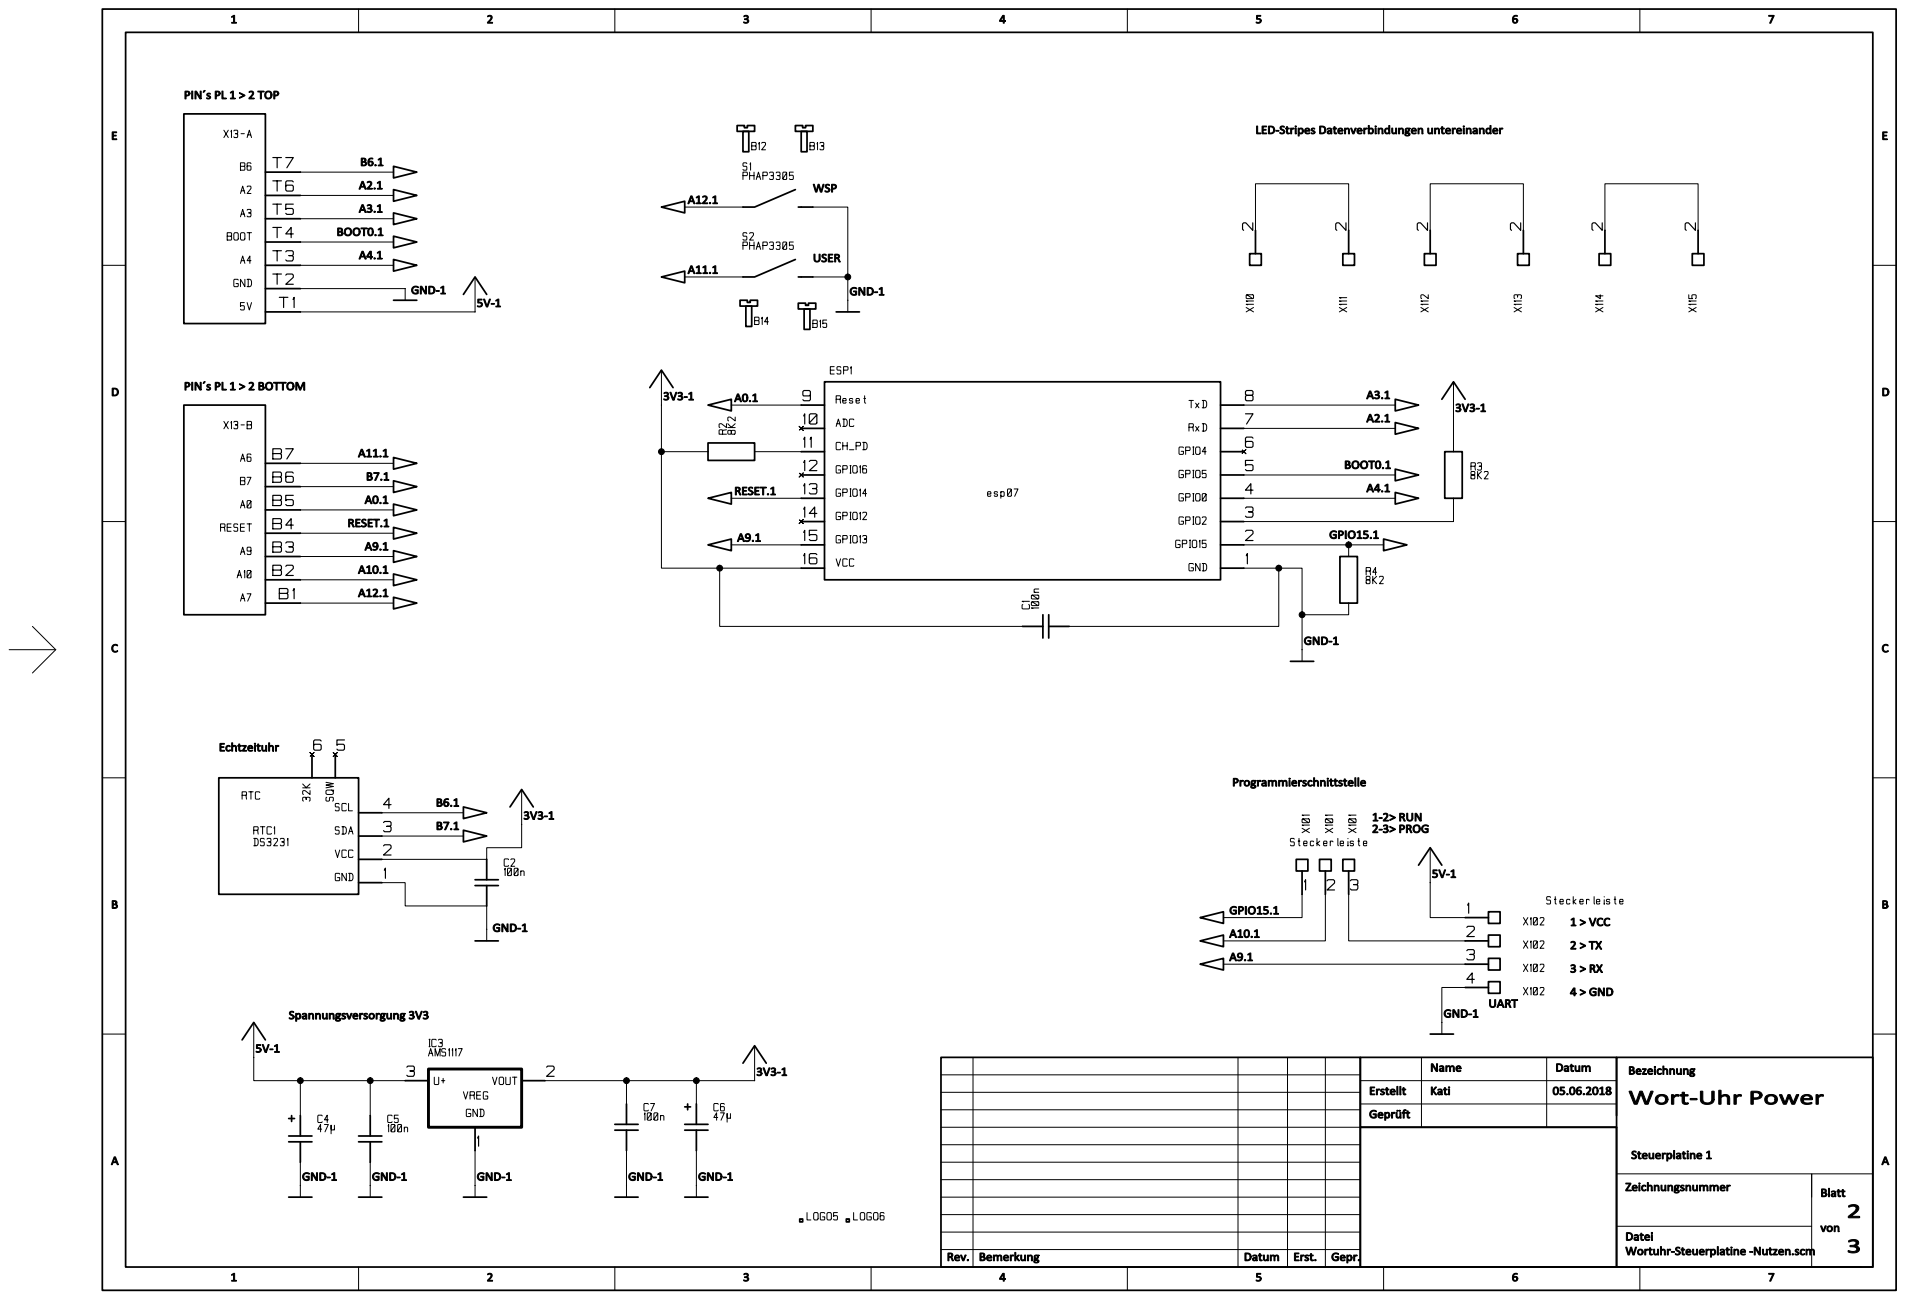
[picture p59: page 2]

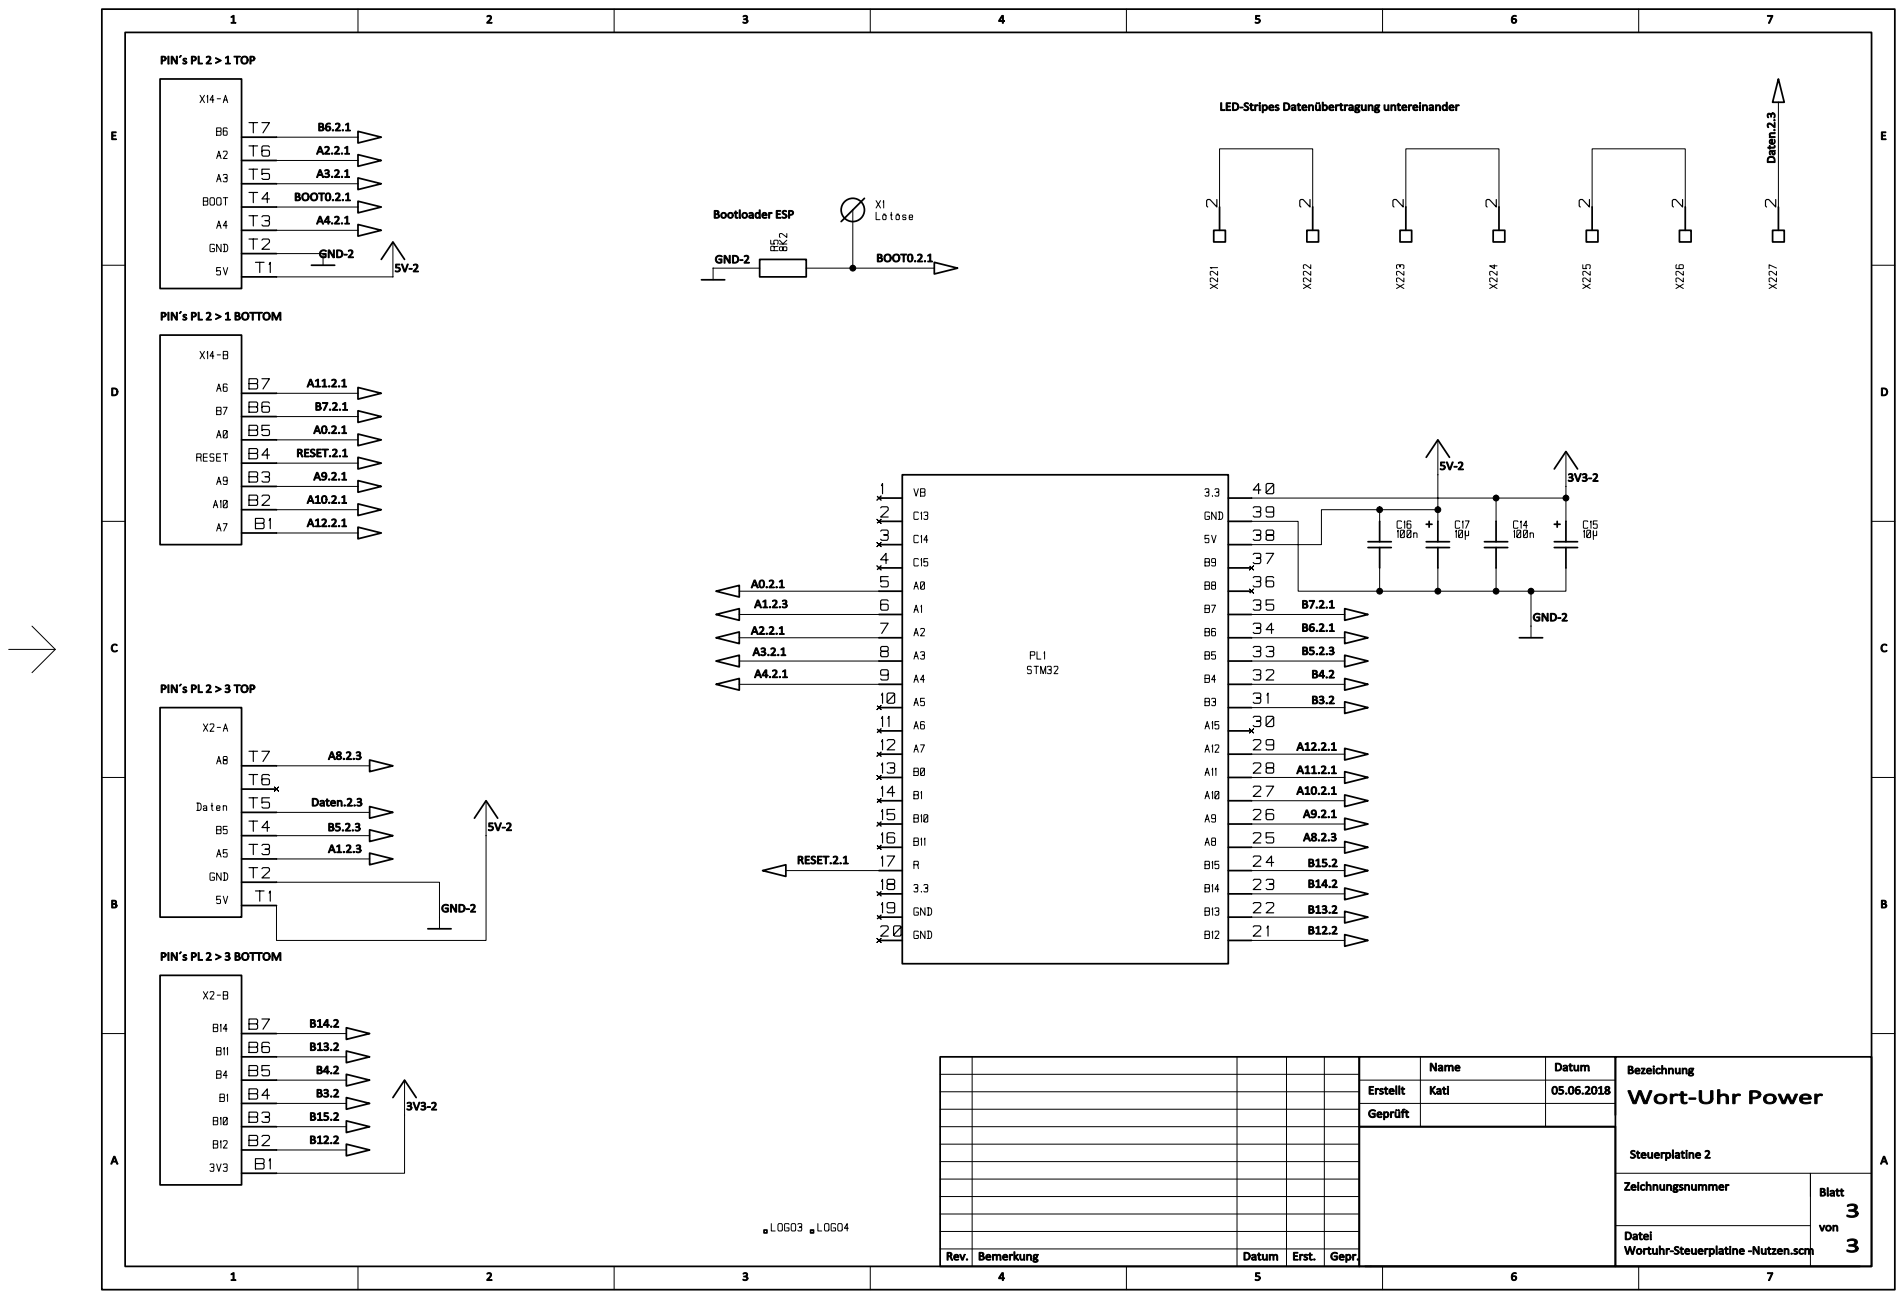
[picture p60: page 3]
