RT-CUSTOMZ/WortUhr/Hardware/Alt/Steuerplatinen Produktionsdaten V1.1/Wortuhr-Steuerplatine-NutzenNEU-ohne BO- Viaplan.pdf

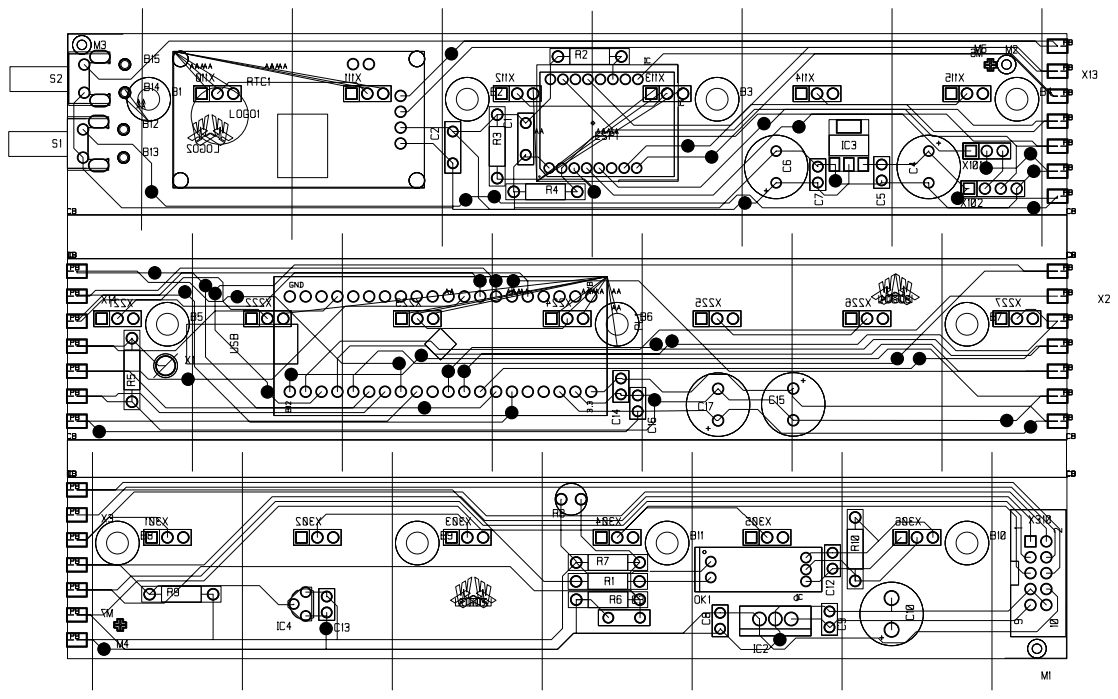
[picture p61: page 1]
