RT-CUSTOMZ/WortUhr/Software/STM32/src/esp8266/esp8266.c

/*---------------------------------------------------------------------------------------------------------------------------------------------------
 * esp8266.c - ESP8266 WLAN routines
 *
 * Copyright (c) 2014-2018 Frank Meyer - frank(at)fli4l.de
 *
 * This program is free software; you can redistribute it and/or modify
 * it under the terms of the GNU General Public License as published by
 * the Free Software Foundation; either version 2 of the License, or
 * (at your option) any later version.
 *---------------------------------------------------------------------------------------------------------------------------------------------------
 */
#include <stdio.h>
#include <stdlib.h>
#include "log.h"
#include "delay.h"
#include "display.h"
#include "esp8266.h"
#include "esp8266-config.h"
#include "io.h"

#undef UART_PREFIX
#define UART_PREFIX                     esp8266
#include "uart.h"

#define MSEC(x)                         (x/10)

#define ESP8266_MAX_SEND_CMD_LEN        120

/*--------------------------------------------------------------------------------------------------------------------------------------
 * globals:
 *--------------------------------------------------------------------------------------------------------------------------------------
 */
volatile uint_fast8_t                   esp8266_ten_ms_tick;            // should be set every 10 msec to 1, see IRQ in main.c

ESP8266_GLOBALS                         esp8266;

#if defined (STM32F407VG)                                               // STM32F4 Discovery Board PD12

#define ESP8266_RST_PERIPH_CLOCK_CMD    RCC_AHB1PeriphClockCmd
#define ESP8266_RST_PERIPH              RCC_AHB1Periph_GPIOC
#define ESP8266_RST_PORT                GPIOC
#define ESP8266_RST_PIN                 GPIO_Pin_5

#define ESP8266_CH_PD_PERIPH_CLOCK_CMD  RCC_AHB1PeriphClockCmd
#define ESP8266_CH_PD_PERIPH            RCC_AHB1Periph_GPIOC
#define ESP8266_CH_PD_PORT              GPIOC
#define ESP8266_CH_PD_PIN               GPIO_Pin_4

#define ESP8266_FLASH_PERIPH_CLOCK_CMD  RCC_AHB1PeriphClockCmd
#define ESP8266_FLASH_PERIPH            RCC_AHB1Periph_GPIOC
#define ESP8266_FLASH_PORT              GPIOC
#define ESP8266_FLASH_PIN               GPIO_Pin_3

#elif defined (STM32F4XX)                                               // STM32F4xx Nucleo Board

#define ESP8266_RST_PERIPH_CLOCK_CMD    RCC_AHB1PeriphClockCmd
#define ESP8266_RST_PERIPH              RCC_AHB1Periph_GPIOA
#define ESP8266_RST_PORT                GPIOA
#define ESP8266_RST_PIN                 GPIO_Pin_7

#define ESP8266_CH_PD_PERIPH_CLOCK_CMD  RCC_AHB1PeriphClockCmd
#define ESP8266_CH_PD_PERIPH            RCC_AHB1Periph_GPIOA
#define ESP8266_CH_PD_PORT              GPIOA
#define ESP8266_CH_PD_PIN               GPIO_Pin_6

#define ESP8266_FLASH_PERIPH_CLOCK_CMD  RCC_AHB1PeriphClockCmd
#define ESP8266_FLASH_PERIPH            RCC_AHB1Periph_GPIOA
#define ESP8266_FLASH_PORT              GPIOA
#define ESP8266_FLASH_PIN               GPIO_Pin_4

#elif defined (STM32F103)

#define ESP8266_RST_PERIPH_CLOCK_CMD    RCC_APB2PeriphClockCmd
#define ESP8266_RST_PERIPH              RCC_APB2Periph_GPIOA
#define ESP8266_RST_PORT                GPIOA
#define ESP8266_RST_PIN                 GPIO_Pin_0

#define ESP8266_CH_PD_PERIPH_CLOCK_CMD  RCC_APB2PeriphClockCmd
#define ESP8266_CH_PD_PERIPH            RCC_APB2Periph_GPIOA
#define ESP8266_CH_PD_PORT              GPIOA
#define ESP8266_CH_PD_PIN               GPIO_Pin_5

#define ESP8266_FLASH_PERIPH_CLOCK_CMD  RCC_APB2PeriphClockCmd
#define ESP8266_FLASH_PERIPH            RCC_APB2Periph_GPIOA
#define ESP8266_FLASH_PORT              GPIOA
#define ESP8266_FLASH_PIN               GPIO_Pin_4

#else
#error STM32 unknown
#endif

#if ESP8266_DEBUG == 1
#undef UART_PREFIX
#define UART_PREFIX     log
#include "uart.h"
#define log_hex(b)      do { char log_buf[5]; sprintf (log_buf, "<%02x>", b); log_uart_puts (log_buf); } while (0)
#else
#define log_init(b)
#define log_putc(c)
#define log_puts(s)
#define log_message(m)
#define log_flush()
#define log_hex(b)
#endif

static void
esp8266_gpio_init (void)
{
    GPIO_InitTypeDef gpio;

    GPIO_StructInit (&gpio);

    ESP8266_RST_PERIPH_CLOCK_CMD (ESP8266_RST_PERIPH, ENABLE);      // enable clock for ESP8266 RST

    gpio.GPIO_Pin   = ESP8266_RST_PIN;
    gpio.GPIO_Speed = GPIO_Speed_2MHz;

#if defined (STM32F10X)
    gpio.GPIO_Mode  = GPIO_Mode_Out_PP;
#elif defined (STM32F4XX)
    gpio.GPIO_Mode  = GPIO_Mode_OUT;
    gpio.GPIO_OType = GPIO_OType_PP;
    gpio.GPIO_PuPd  = GPIO_PuPd_NOPULL;
#endif

    GPIO_Init(ESP8266_RST_PORT, &gpio);

    ESP8266_RST_PERIPH_CLOCK_CMD (ESP8266_CH_PD_PERIPH, ENABLE);    // enable clock for ESP8266 CH_PD

    gpio.GPIO_Pin   = ESP8266_CH_PD_PIN;
    gpio.GPIO_Speed = GPIO_Speed_2MHz;

#if defined (STM32F10X)
    gpio.GPIO_Mode  = GPIO_Mode_Out_PP;
#elif defined (STM32F4XX)
    gpio.GPIO_Mode  = GPIO_Mode_OUT;
    gpio.GPIO_OType = GPIO_OType_PP;
    gpio.GPIO_PuPd  = GPIO_PuPd_NOPULL;
#endif

    GPIO_Init(ESP8266_CH_PD_PORT, &gpio);

    ESP8266_RST_PERIPH_CLOCK_CMD (ESP8266_FLASH_PERIPH, ENABLE);    // enable clock for ESP8266 FLASH

    gpio.GPIO_Pin   = ESP8266_FLASH_PIN;
    gpio.GPIO_Speed = GPIO_Speed_2MHz;

#if defined (STM32F10X)
    gpio.GPIO_Mode  = GPIO_Mode_Out_PP;
#elif defined (STM32F4XX)
    gpio.GPIO_Mode  = GPIO_Mode_OUT;
    gpio.GPIO_OType = GPIO_OType_PP;
    gpio.GPIO_PuPd  = GPIO_PuPd_NOPULL;
#endif

    GPIO_Init(ESP8266_FLASH_PORT, &gpio);

    GPIO_SET_BIT(ESP8266_RST_PORT,   ESP8266_RST_PIN);
    GPIO_SET_BIT(ESP8266_CH_PD_PORT, ESP8266_CH_PD_PIN);
    GPIO_SET_BIT(ESP8266_FLASH_PORT, ESP8266_FLASH_PIN);
}
/*--------------------------------------------------------------------------------------------------------------------------------------
 * INTERN: poll ESP8266
 *--------------------------------------------------------------------------------------------------------------------------------------
 */
static uint_fast8_t
esp8266_poll (uint_fast8_t * chp, uint_fast16_t ten_ms)
{
    uint_fast16_t  cnt = 0;

    esp8266_ten_ms_tick = 0;

    while (1)
    {
        if (esp8266_uart_poll (chp))
        {
            return 1;
        }

        if (esp8266_ten_ms_tick)
        {
            esp8266_ten_ms_tick = 0;

            cnt++;

            if (cnt >= ten_ms)
            {
                break;
            }
        }
    }
    return 0;
}

/*--------------------------------------------------------------------------------------------------------------------------------------
 * get message from ESP8266
 *--------------------------------------------------------------------------------------------------------------------------------------
 */
uint_fast8_t
esp8266_get_message (void)
{
    static char         answer[ESP8266_MAX_ANSWER_LEN + 1];
    static uint_fast8_t answer_pos = 0;
    uint_fast8_t        ch;
    uint_fast8_t        rtc = ESP8266_TIMEOUT;

    log_flush ();
    esp8266_uart_flush ();

    if (esp8266_uart_char_available ())
    {
        while (1)
        {
            if (esp8266_uart_poll (&ch) == 0)                                 // don't wait
            {
                rtc = ESP8266_TIMEOUT;
                break;
            }

            esp8266.is_up = 1;

            if (ch == '\n')
            {
                answer[answer_pos] = '\0';

                if (answer_pos > 0)
                {
                    answer_pos = 0;

                    if (answer[0] == '.' && answer[1] == '\0')                              // dot as "silent ok"
                    {
                        rtc = ESP8266_OK;
                        break;
                    }
                    else if (! strncmp (answer, "FILE ", 5))                                // FILE: keep silent
                    {
                        strncpy (esp8266.u.filedata, answer + 5, ESP8266_MAX_CMD_LEN);
                        rtc = ESP8266_FILEDATA;
                        break;
                    }
                    else if (! strncmp (answer, "ICON ", 5))                                // ICON: keep silent
                    {
                        strncpy (esp8266.u.filedata, answer + 5, ESP8266_MAX_CMD_LEN);
                        rtc = ESP8266_ICONDATA;
                        break;
                    }
                    else if (! strncmp (answer, "TAB", 3))                                  // TABxxx: keep silent
                    {
                        if (! strcmp (answer, "TABLES"))                                    // TABINFO
                        {
                            rtc = ESP8266_TABLES;
                            break;
                        }
                        else if (! strncmp (answer + 3, "INFO ", 5))                        // TABINFO
                        {
                            strncpy (esp8266.u.tabinfo, answer + 8, ESP8266_TABINFO_LEN);
                            esp8266.u.tabinfo[ESP8266_TABINFO_LEN] = '\0';
                            rtc = ESP8266_TABINFO;
                            break;
                        }
                        else if (! strncmp (answer + 3, "ILLU ", 5))                        // TABILLU
                        {
                            strncpy (esp8266.u.tabillu, answer + 8, ESP8266_TABILLU_LEN);
                            esp8266.u.tabillu[ESP8266_TABILLU_LEN] = '\0';
                            rtc = ESP8266_TABILLU;
                            break;
                        }
#if WCLOCK24H == 1
                        else if (! strncmp (answer + 3, "T ", 2))                           // TABT
                        {
                            strncpy (esp8266.u.tabt, answer + 5, ESP8266_TABT_LEN);
                            esp8266.u.tabt[ESP8266_TABT_LEN] = '\0';
                            rtc = ESP8266_TABT;
                            break;
                        }
#endif
                        else if (! strncmp (answer + 3, "H ", 2))                           // TABH
                        {
                            strncpy (esp8266.u.tabh, answer + 5, ESP8266_TABH_LEN);
                            esp8266.u.tabh[ESP8266_TABH_LEN] = '\0';
                            rtc = ESP8266_TABH;
                            break;
                        }
                        else if (! strncmp (answer + 3, "M ", 2))                           // TABM
                        {
                            strncpy (esp8266.u.tabm, answer + 5, ESP8266_TABM_LEN);
                            esp8266.u.tabm[ESP8266_TABM_LEN] = '\0';
                            rtc = ESP8266_TABM;
                            break;
                        }
                        else
                        {
                            rtc = ESP8266_UNSPECIFIED;
                            break;
                        }
                    }
                    else
                    {
                        log_puts ("(");
                        log_puts (answer);
                        log_puts (")\r\n");
                        log_flush ();

                        if (! strncmp (answer, "OK", 2))
                        {
                            rtc = ESP8266_OK;
                            break;
                        }
                        else if (! strncmp (answer, "ERROR", 5))
                        {
                            rtc = ESP8266_ERROR;
                            break;
                        }
                        else if (! strncmp (answer, "- ", 2))
                        {
                            rtc = ESP8266_DEBUGMSG;
                            break;
                        }
                        else if (! strncmp (answer, "IPADDRESS ", 10))
                        {
                            strncpy (esp8266.ipaddress, answer + 10, ESP8266_MAX_IPADDRESS_LEN);
                            esp8266.is_online = 1;
                            rtc = ESP8266_IPADDRESS;
                            break;
                        }
                        else if (! strncmp (answer, "AP ", 3))
                        {
                            strncpy (esp8266.accesspoint, answer + 3, ESP8266_MAX_ACCESSPOINT_LEN);
                            rtc = ESP8266_ACCESSPOINT;
                            break;
                        }
                        else if (! strncmp (answer, "MODE ", 5))
                        {
                            if (! strncmp (answer + 5, "ap", 2))
                            {
                                esp8266.mode = ESP8266_AP_MODE;
                            }
                            else
                            {
                                esp8266.mode = ESP8266_CLIENT_MODE;
                            }
                            rtc = ESP8266_MODE;
                            break;
                        }
                        else if (! strncmp (answer, "TIME ", 5))
                        {
                            strncpy (esp8266.u.time, answer + 5, ESP8266_MAX_TIME_LEN);
                            rtc = ESP8266_TIME;
                            break;
                        }
                        else if (! strncmp (answer, "WEATHER ", 8))
                        {
                            strncpy (esp8266.u.weather, answer + 8, ESP8266_MAX_WEATHER_LEN);
                            rtc = ESP8266_WEATHER;
                            break;
                        }
                        else if (! strncmp (answer, "WEATHER_FC ", 11))
                        {
                            strncpy (esp8266.u.weather, answer + 11, ESP8266_MAX_WEATHER_LEN);
                            rtc = ESP8266_WEATHER_FC;
                            break;
                        }
                        else if (! strncmp (answer, "WICON ", 6))
                        {
                            strncpy (esp8266.u.weather, answer + 6, 2);                         // copy only 2 characters ("02d" -> "02")
                            esp8266.u.weather[2] = '\0';
                            rtc = ESP8266_WEATHER_ICON;
                            break;
                        }
                        else if (! strncmp (answer, "WICON_FC ", 9))
                        {
                            strncpy (esp8266.u.weather, answer + 9, 2);                         // copy only 2 characters ("02d" -> "02")
                            esp8266.u.weather[2] = '\0';
                            rtc = ESP8266_WEATHER_FC_ICON;
                            break;
                        }
                        else if (! strncmp (answer, "FIRMWARE ", 9))
                        {
                            strncpy (esp8266.firmware, answer + 9, ESP8266_MAX_FIRMWARE_LEN);
                            rtc = ESP8266_FIRMWARE;
                            break;
                        }
                        else if (! strncmp (answer, "CMD ", 4))
                        {
                            strncpy (esp8266.u.cmd, answer + 4, ESP8266_MAX_CMD_LEN);
                            rtc = ESP8266_CMD;
                            break;
                        }
                        else if (! strncmp (answer, "OPEN ", 5))
                        {
                            strncpy (esp8266.u.filedata, answer + 5, ESP8266_MAX_CMD_LEN);
                            rtc = ESP8266_FILEOPEN;
                            break;
                        }
                        else if (! strncmp (answer, "FILE ", 5))
                        {
                            strncpy (esp8266.u.filedata, answer + 5, ESP8266_MAX_CMD_LEN);
                            rtc = ESP8266_FILEDATA;
                            break;
                        }
                        else if (! strcmp (answer, "CLOSE"))
                        {
                            rtc = ESP8266_FILECLOSE;
                            break;
                        }
                        else
                        {
                            rtc = ESP8266_UNSPECIFIED;
                            break;
                        }
                    }
                }
                else // l == 0
                {
                    log_flush ();
                }
            }
            else if (ch == '\r')
            {
                ;
            }
            else if (answer_pos < ESP8266_MAX_ANSWER_LEN)
            {
                answer[answer_pos++] = ch;
            }
        }
    }

    if (rtc != ESP8266_TIMEOUT)
    {
        answer[0] = '\0';
    }
    return rtc;
}

/*--------------------------------------------------------------------------------------------------------------------------------------
 * send a command to ESP8266
 *--------------------------------------------------------------------------------------------------------------------------------------
 */
void
esp8266_send_cmd (const char * cmd, const char * args, uint_fast8_t do_log)
{
    uint_fast8_t    length;
    uint_fast8_t    ch;
    uint_fast8_t    i;

    if (do_log)
    {
        log_puts ("--> ");

        length = strlen (cmd);

        for (i = 0; i < length; i++)
        {
            ch = cmd[i];

            if (ch >= 32 && ch < 127)
            {
                log_putc (ch);
            }
            else
            {
                log_hex (ch);
            }
        }

        if (args)
        {
            log_putc (' ');
            log_putc ('"');

            length = strlen (args);

            for (i = 0; i < length; i++)
            {
                ch = args[i];

                if (ch >= 32 && ch < 127)
                {
                    log_putc (ch);
                }
                else
                {
                    log_hex (ch);
                }
            }
            log_putc ('"');
        }

        log_puts ("<0d><0a>\r\n");
        log_flush ();
    }

    esp8266_uart_puts (cmd);

    if (args)
    {
        esp8266_uart_putc (' ');
        esp8266_uart_putc ('"');
        esp8266_uart_puts (args);
        esp8266_uart_putc ('"');
    }

    esp8266_uart_puts ("\r\n");
    esp8266_uart_flush();
}

/*--------------------------------------------------------------------------------------------------------------------------------------
 * send (http) data to ESP8266
 *--------------------------------------------------------------------------------------------------------------------------------------
 */
void
esp8266_send_data (unsigned char * data, uint_fast8_t len)
{
    uint_fast8_t    i;

    for (i = 0; i < len; i++)
    {
        esp8266_uart_putc (data[i]);
    }

    esp8266_uart_flush ();

    return;
}

/*--------------------------------------------------------------------------------------------------------------------------------------
 * reset ESP8266
 *--------------------------------------------------------------------------------------------------------------------------------------
 */
void
esp8266_reset (void)
{
    uint_fast8_t    ch;

    GPIO_RESET_BIT(ESP8266_RST_PORT, ESP8266_RST_PIN);
    delay_msec (50);
    GPIO_SET_BIT(ESP8266_RST_PORT, ESP8266_RST_PIN);

    while (esp8266_poll (&ch, MSEC(500)))                                   // eat boot message stuff
    {
        ;
    }
}

/*--------------------------------------------------------------------------------------------------------------------------------------
 * power down ESP8266
 *--------------------------------------------------------------------------------------------------------------------------------------
 */
void
esp8266_powerdown (void)
{
    GPIO_RESET_BIT(ESP8266_CH_PD_PORT, ESP8266_CH_PD_PIN);
}

/*--------------------------------------------------------------------------------------------------------------------------------------
 * power up ESP8266
 *--------------------------------------------------------------------------------------------------------------------------------------
 */
void
esp8266_powerup (void)
{
    GPIO_SET_BIT(ESP8266_CH_PD_PORT, ESP8266_CH_PD_PIN);
}

/*--------------------------------------------------------------------------------------------------------------------------------------
 * connect to access point
 *--------------------------------------------------------------------------------------------------------------------------------------
 */
void
esp8266_connect_to_access_point (char * ssid, char * key)
{
    char send_cmd_buf[ESP8266_MAX_SEND_CMD_LEN + 1];

    esp8266.ipaddress[0] = '\0';
    esp8266.is_online = 0;

    sprintf (send_cmd_buf, "cap \"%s\",\"%s\"", ssid, key);
    esp8266_send_cmd (send_cmd_buf, (const char *) NULL, 1);
}

/*--------------------------------------------------------------------------------------------------------------------------------------
 * start as access point
 *--------------------------------------------------------------------------------------------------------------------------------------
 */
void
esp8266_accesspoint (const char * ssid, const char * key)
{
    char send_cmd_buf[ESP8266_MAX_SEND_CMD_LEN + 1];

    esp8266.ipaddress[0] = '\0';
    esp8266.is_online = 0;

    sprintf (send_cmd_buf, "ap \"%s\",\"%s\"", ssid, key);
    esp8266_send_cmd (send_cmd_buf, (const char *) NULL, 1);
}

/*--------------------------------------------------------------------------------------------------------------------------------------
 * start WPS
 *--------------------------------------------------------------------------------------------------------------------------------------
 */
void
esp8266_wps (void)
{
    esp8266.ipaddress[0] = '\0';
    esp8266.is_online = 0;

    esp8266_send_cmd ("wps", (const char *) NULL, 1);
}

/*--------------------------------------------------------------------------------------------------------------------------------------
 * set ESP8266 into flash mode and copy all characters from extern logger UART to ESP8266 UART
 *--------------------------------------------------------------------------------------------------------------------------------------
 */
void
esp8266_flash (void)
{
    uint_fast8_t    ch;

    log_init (115200);
    esp8266_gpio_init ();
    esp8266_uart_init (115200);

    GPIO_RESET_BIT(ESP8266_FLASH_PORT, ESP8266_FLASH_PIN);
    GPIO_RESET_BIT(ESP8266_RST_PORT, ESP8266_RST_PIN);
    delay_msec (50);                                                                        // wait 50 msec
    GPIO_SET_BIT(ESP8266_RST_PORT, ESP8266_RST_PIN);
    delay_msec (500);                                                                       // wait 500 msec
    GPIO_SET_BIT(ESP8266_FLASH_PORT, ESP8266_FLASH_PIN);

    while (1)
    {
        if (esp8266_uart_poll (&ch))
        {
            log_uart_putc (ch);
        }

        if (log_uart_poll (&ch))
        {
            esp8266_uart_putc (ch);
        }
    }
}

/*--------------------------------------------------------------------------------------------------------------------------------------
 * initialize UART and ESP8266
 *--------------------------------------------------------------------------------------------------------------------------------------
 */
void
esp8266_init (void)
{
    static uint_fast8_t     already_called;

    if (! already_called)
    {
        already_called = 1;

        log_init (115200);
        log_puts ("ESP8266 LOGGER\r\n");

        esp8266_gpio_init ();
        esp8266_uart_init (115200);
        esp8266_reset ();
    }

    return;
}
